michaelerule/goggles/hardware/pcb/Attiny14:24:84/eagle/index.html

### Index of eagle

../
board.zip
eagle.epf
gog2.b#1
gog2.b#2
gog2.brd
gog2.s#1
gog2.s#2
gog2.sch
Goggles.b#1
Goggles.brd
Goggles.s#1
Goggles.sch
goggles_eagle.zip
instructions
