michaelerule/goggles/tools/ee cheatsheet/media/circuitcheatsheet.odt

Circuit diagram cheat shee

t

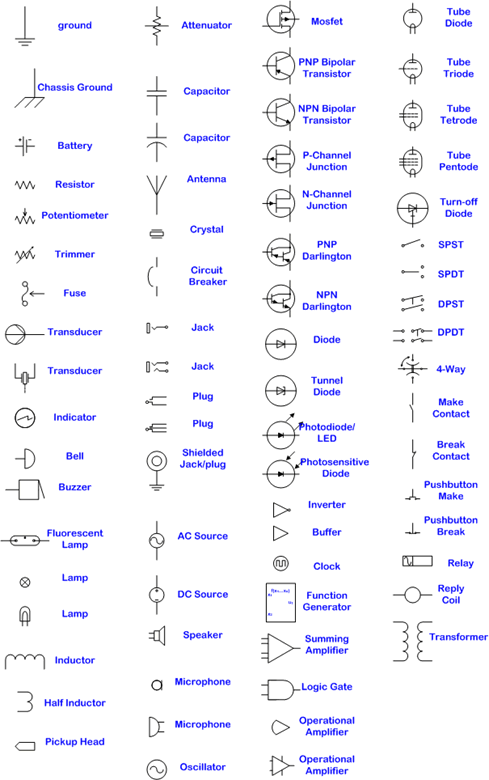
[picture p3: figure]
