michaelerule/goggles/tools/ee cheatsheet/media/LED.odt

LED and resistor cheat sheet

Wavelength (nm) | Color | Voltage | Resistor 3.3v | Resistor 5v
940 | Infrared | 1.5 | 100 | 180
880 | Infrared | 1.7 | 82 …
850 | Infrared
660 | Ultra Red | 1.8
635 | High Eff. Red | 2 | 68 … | 150
633 | Super Red | 2.2 | 56 …
620 | Super Orange
612 | Super Orange
605 | Orange | 2.1
595 | Super Yellow | 2.2
592 | Super Pure Yellow | 2.1
585 | Yellow
4500K | Incandescent White | 3.6 | none | 82 …
6500K | Pale White
8000K | Cool White
574 | Super Lime Yellow | 2.4 | 47 … | 150
570 | Super Lime Green | 2 | 68 …
565 | High Eff. Green | 2.1
560 | Super Pure Green
555 | Pure Green
525 | Aqua Green | 3.5 | none | 82 …
505 | Blue Green
470 | Super Blue | 3.6
430 | Ultra Blue | 3.8 | none | 68 …

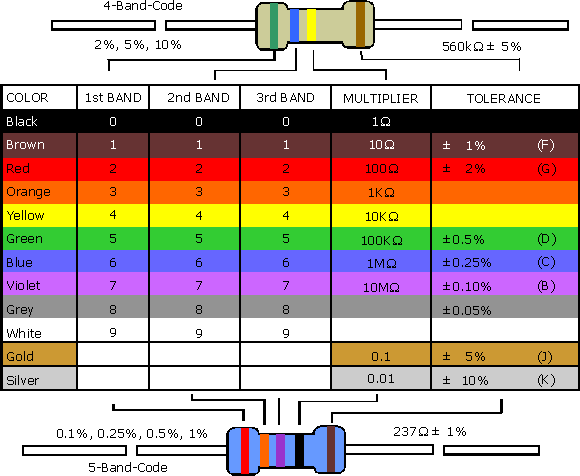
[picture p4: figure]
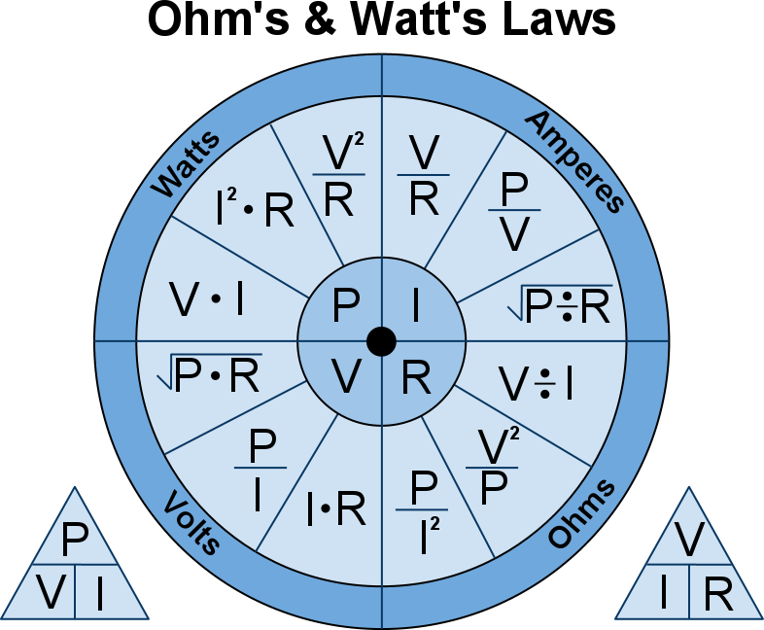
[picture p5: figure]
