michaelerule/goggles/documentation/laymanflicker/flicker_layman.odt

Geometric hallucinations induced by flickering light

Most people see colorful geometric patterns when looking at uniform flickering lights of a certain frequency. These patterns are subjectively described as “checkerboards” “ripples” “starbursts” “honeycombs”, sometimes taking on an overall tunnel-like appearance. It is striking how universal these patterns are – these simple flicker-induced geometric hallucinations are similar across individuals, and similar to certain visual hallucinations seen in visual-triggered epilepsy, migraine auras, and hallucinogens. A simple way to achieve such hallucinations is to close one's eyes and face toward the sun. Then, with fingers outstretched and separated, wave the hand back and forth in front of the eyes. Your fingers will create a flickering of the sunlight, which will be diffused and made uniform by closed eyelids.

The shortest primer on the brain and visual system ever

To understand why flickering lights might trigger geometric hallucinations, and why the hallucinations should take on particular forms, we need to understand a little about the nervous system. A good review is beyond the scope of this article, but I attempt to give a short overview here.

Very briefly, the eye and the brain contain cells called neurons which are specialized for computation. Neurons communicate with each other in little all-or-nothing events called action potentials or “spikes”, which propagate along long “wires” called axons, extending away from the cell body. These spikes are picked up by other neurons with more local tree of wires called “dendrites”. When discussing a large number of neurons, people sometime just think of their average “firing rate” or “activity”, rather than individual spikes.

Early visual processing relates to the sort of geometric hallucinations that we can get out of the early visual system. Light enters the eyes and is picked up by photoreceptor cells. These cells communicate to neurons in the retina that compress visual input. We will focus on four aspects of this compression related to flicker induced geometric visual hallucinations:

1. The RGB color-space picked up by the photo-receptors is converted to three contrasts : light-dark, yellow-blue, and red-green. The color-space conversion relates to how, for instance, a red-green flicker is especially effective at eliciting hallucinations.
2. The image is converted to a form focusing on edges and contrasts – uniform areas are ignored. This band-pass nature of early visual processing relates to how neurons are connected in the visual cortex, which in turns determines what size “waves” might appear in geometric visual hallucinations.
3. The retina has band-pass properties in time as well: slowly changing visual inputs are not registered. This is important for the temporal aspect of flicker induced hallucinations. Certain speeds of flickering will be picked up and transmitted better.
4. The eye has the greatest resolution in the very center, and the resolution drops off toward the periphery. This is why, for example, it is difficult to read things out of the corner of your eye. The brain also devotes less space to processing the periphery. The way that the visual field is “unfolded” in the brain determines the subjective appearance of spontaneous ( hallucinated ) neural activity.

A theory of geometric visual hallucinations

A theory on the origin of geometric visual hallucinations comes from Ermentrout and Cowen (1979), and briefly, makes the following hypotheses:

- The tunnel-like appearance of the overall hallucination relates to how the brain maps the visual field.
- Patterns like checkerboards and honeycombs arise from superposition of multiple waves
- Local interactions in the brain generate wave-like patterns of activity

The two halves of the visual field are split apart and each processed in one half of the brain. The brain devotes more processing power toward the center of the visual field. The net effect is to “unfold” the circular visual field from the retina into a “strip” of the brain at the back called the primary visual cortex. The result is that tunnel-like visual inputs map to simple regular patterns in the brain, and the inverse: hallucinated simple regular patterns in visual cortex are subjectively experienced as tunnel-like visual inputs.

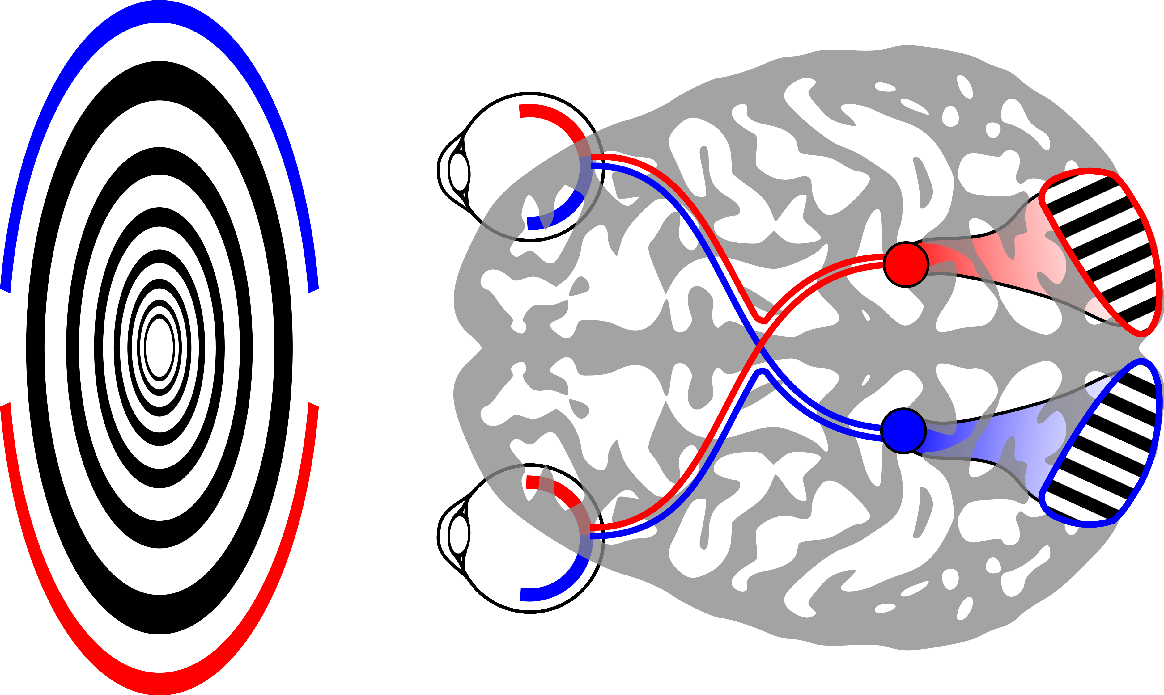
[picture p15: figure]
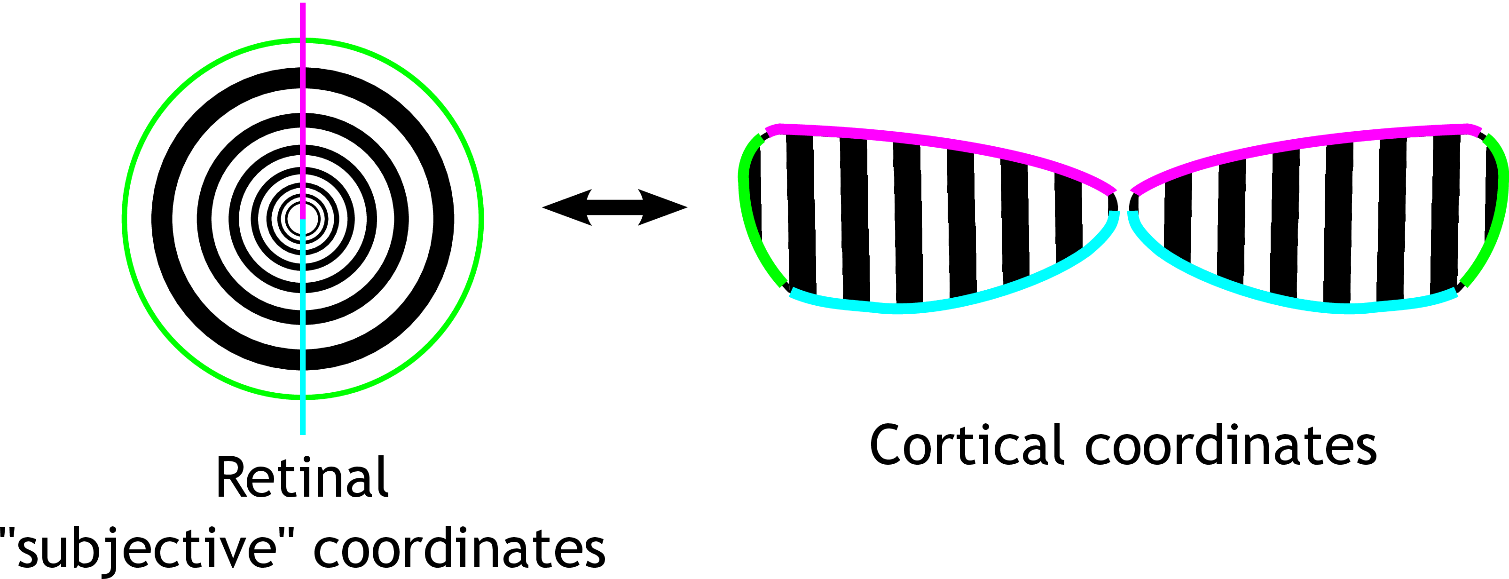
[picture p16: figure]

Stripe-like waves of activity in the brain are sufficient to explain circular, spiral, and starburst hallucinations. Checkerboards can be explained as the sum of two waves at right-angles, and honeycombs can be explains as the sum of three evenly spaced plane waves.

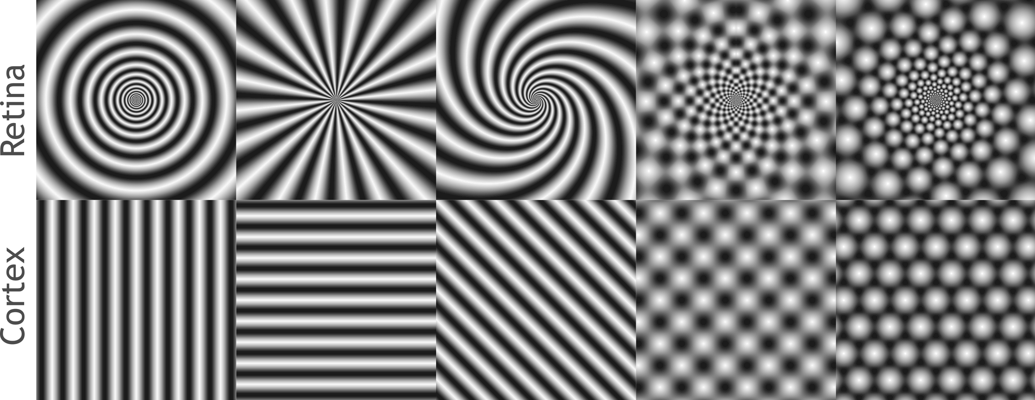
[picture p17: figure]

As to why the brain should spontaneously form waves of activity – that is something of an open question. Qualitatively, one can of it as the brain trying to “find” patterns in an image. Under certain circumstances, the pattern finding circuitry becomes unstable, and tends toward these simple, wave-like patterns.

Driving the brain with a uniform, flickering input

Flickering light is believed to excite patterns using a resonance effect that pushes visual cortex outside of its normal operation. Neural activity in the brain oscillates spontaneously. There is a natural 8-12Hz oscillation in the visual system called the “alpha rhythm”. Providing visual input at this frequency is believed to excite this intrinsic oscillation. Other frequencies work as well, and may interact with other intrinsic oscillations. Stimulation at 8-25Hz also works to excite the alpha oscillation. Even though this is twice the intrinsic frequency of the system, local patches of the brain are hypothesized to respond only to every-other oscillation cycle, effectively oscillating at alpha. These frequencies vary from person to person, and there may be other processes contributing to flicker hallucinations that we have yet to understand.

Why does making visual cortex “resonate” with a stimulus lead to pattern formation? The technical details of why this might happen are beyond the scope of this article – they involve assumptions about how neurons in visual cortex talk to each other, and mathematics to test whether patterned modes are favorable when forcing visual cortex with a uniform periodic stimulus. The qualitative idea is actually quite simple. For analogy, consider shaking a tray of water up and down. Even though you are forcing the whole tray uniformly, if you hit the right frequencies, you can create standing waves in the tray of water. The visual cortex does something similar when you hit it with flickering light.
