michaelerule/goggles/media/art/p (copy).png

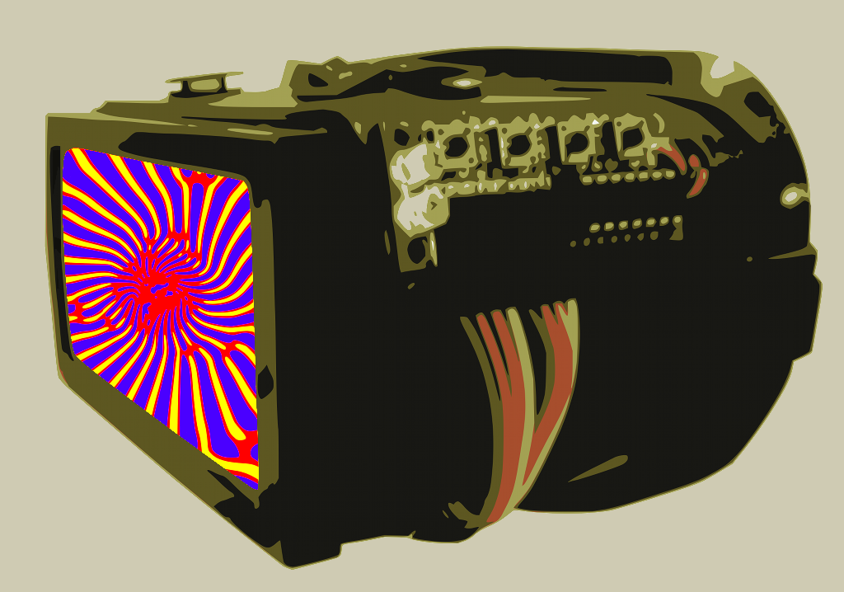
media/art/p (copy).png
