michaelerule/goggles/media/art/the goggs2.png

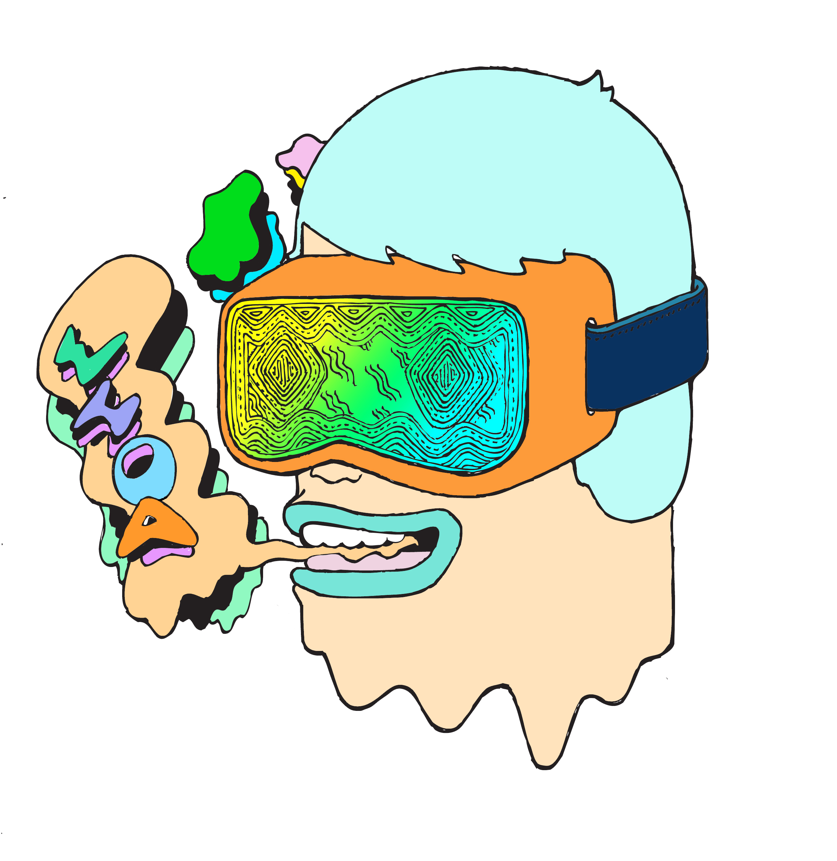
media/art/the goggs2.png
