michaelerule/goggles/media/artwork/2.png

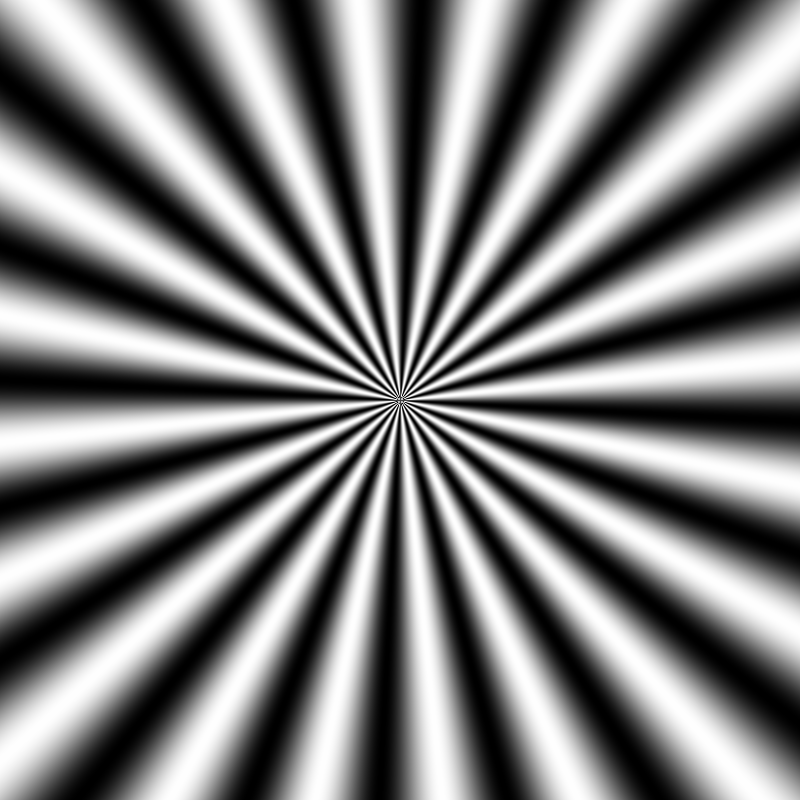
media/artwork/2.png
