michaelerule/goggles/media/artwork/3.png

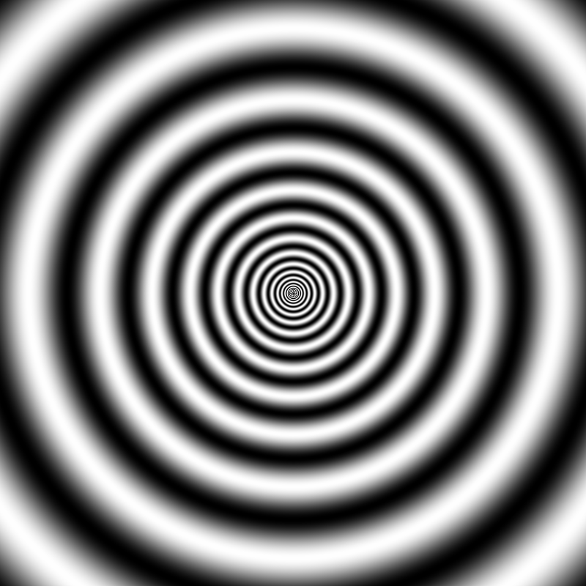
media/artwork/3.png
