michaelerule/goggles/media/artwork/4.png

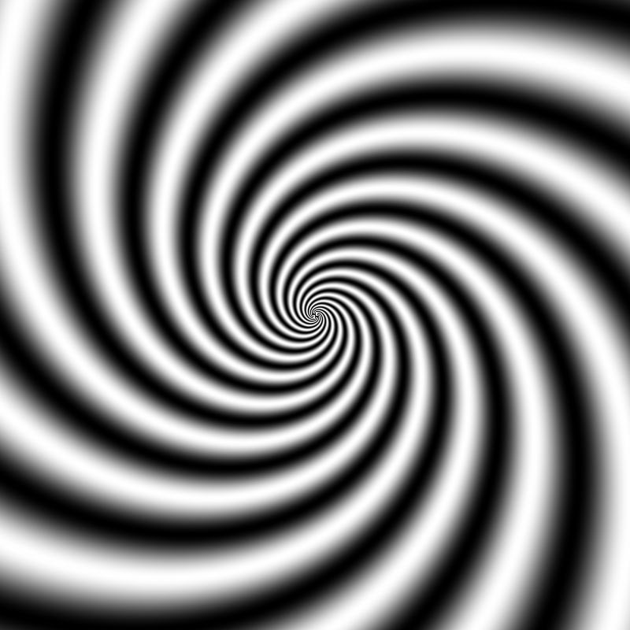
media/artwork/4.png
