michaelerule/goggles/media/artwork/DSCF3299 (copy).JPG

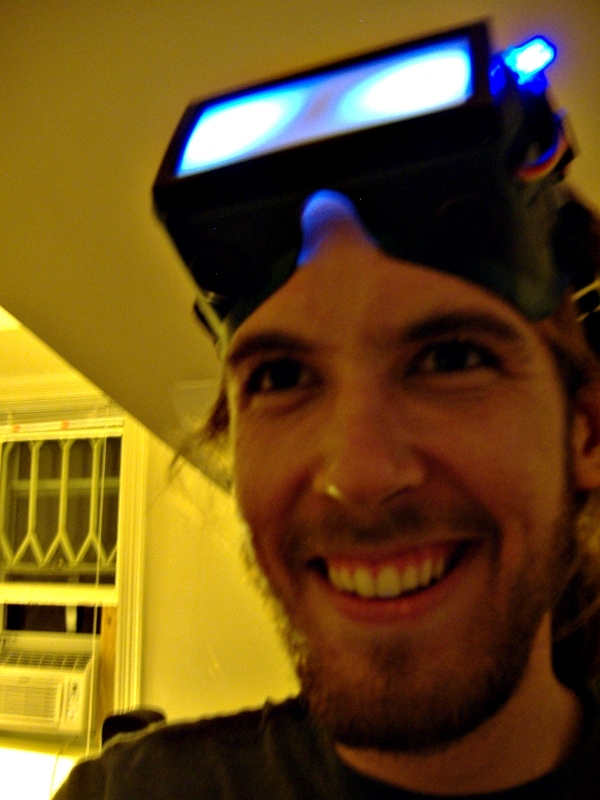
media/artwork/DSCF3299 (copy).JPG
