michaelerule/goggles/media/artwork/DSCF3302 (another copy).JPG.png

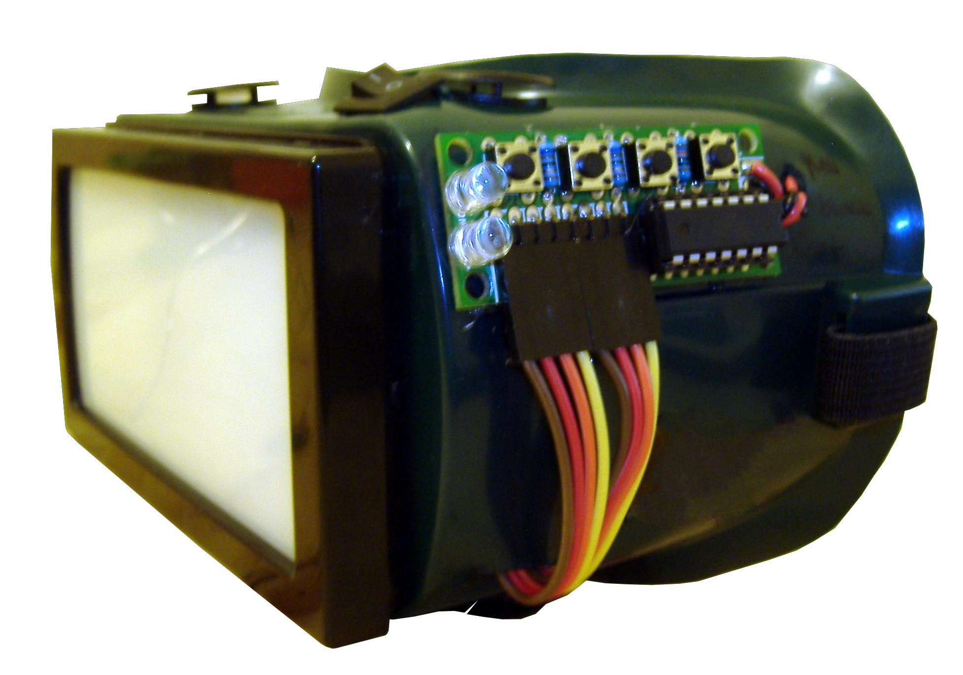
media/artwork/DSCF3302 (another copy).JPG.png
