michaelerule/goggles/media/artwork/out3-30109.png

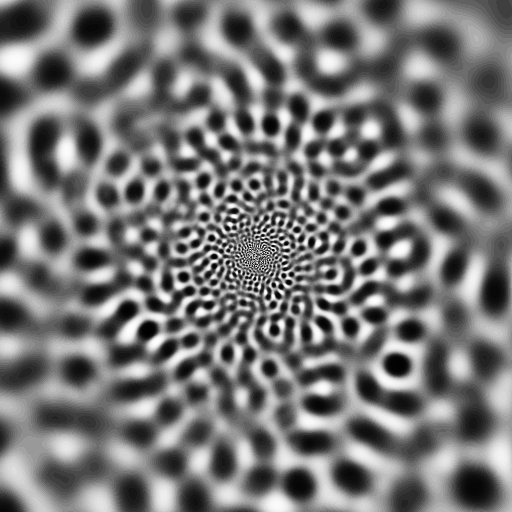
media/artwork/out3-30109.png
