michaelerule/goggles/media/artwork/out3-30433.png

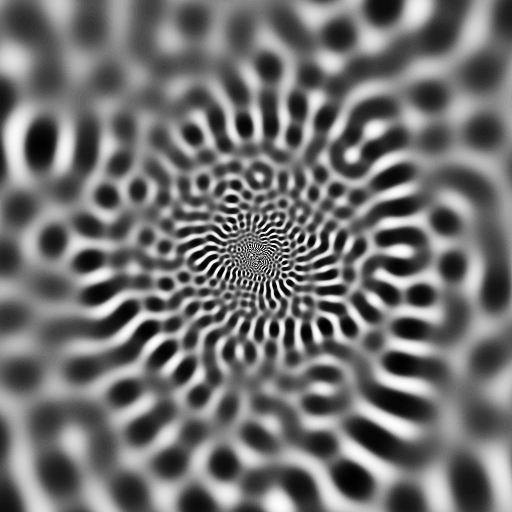
media/artwork/out3-30433.png
