michaelerule/goggles/media/artwork/out3-30541.png

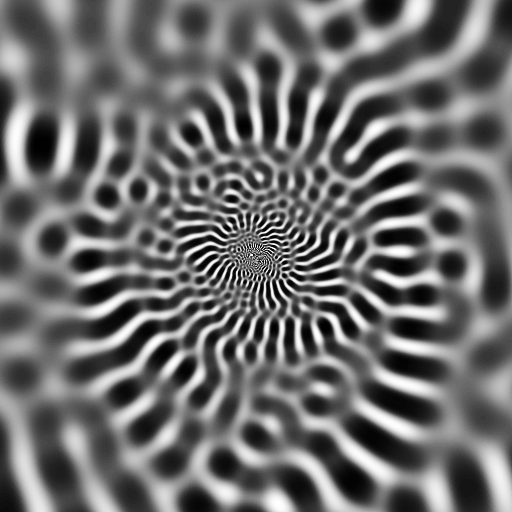
media/artwork/out3-30541.png
