michaelerule/goggles/media/artwork/out3-30649.png

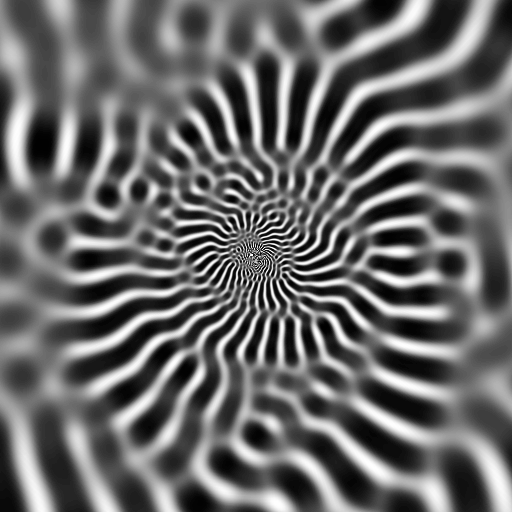
media/artwork/out3-30649.png
