michaelerule/goggles/media/artwork/out3-30757.png

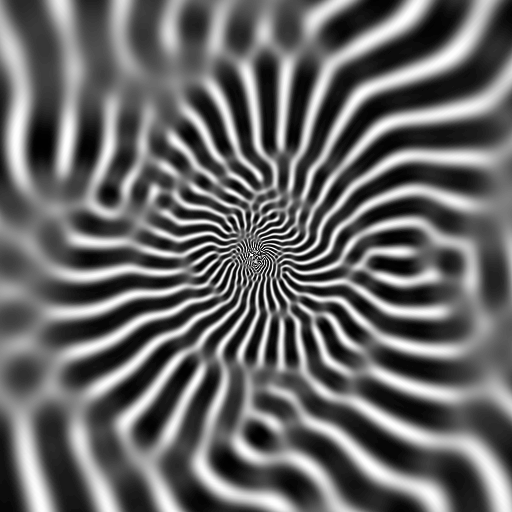
media/artwork/out3-30757.png
