michaelerule/goggles/media/artwork/out3-31729.png

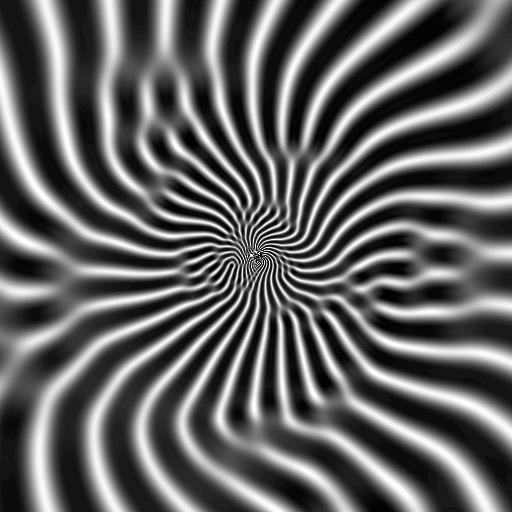
media/artwork/out3-31729.png
