michaelerule/goggles/media/artwork/theory.gif

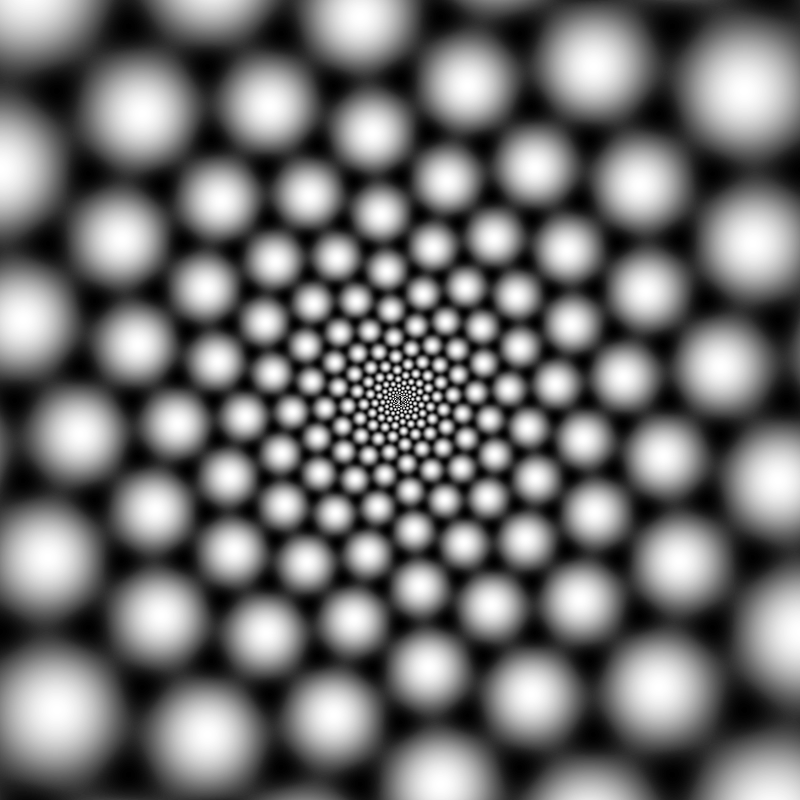
media/artwork/theory.gif
