michaelerule/goggles/media/photos/DSCF3150.JPG

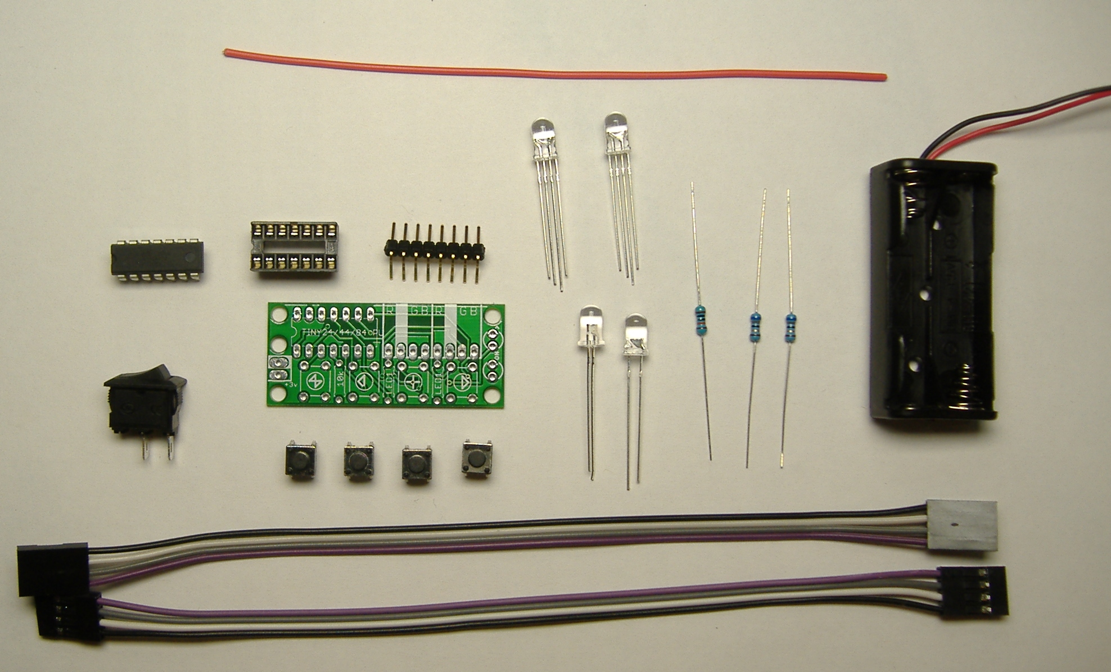
media/photos/DSCF3150.JPG
