michaelerule/goggles/media/photos/DSCF3152.JPG

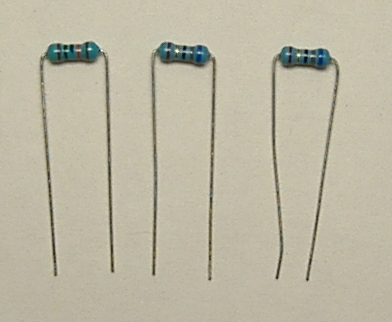
media/photos/DSCF3152.JPG
