michaelerule/goggles/media/photos/DSCF3153.JPG

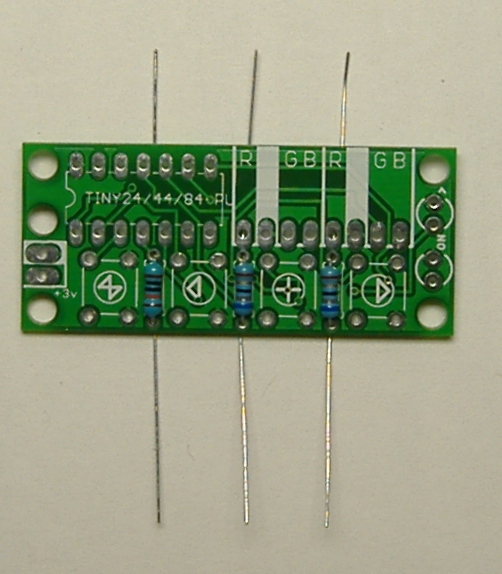
media/photos/DSCF3153.JPG
