michaelerule/goggles/media/photos/DSCF3162.JPG

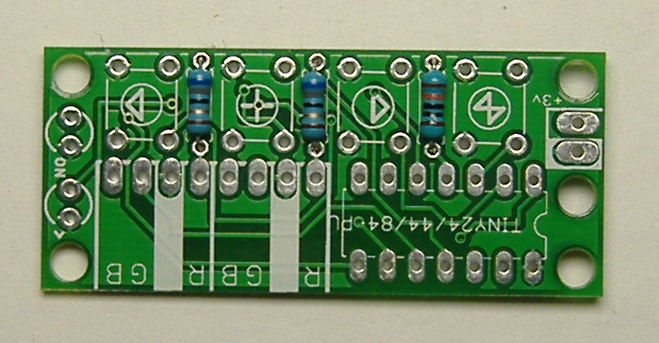
media/photos/DSCF3162.JPG
