michaelerule/goggles/media/photos/DSCF3163.JPG

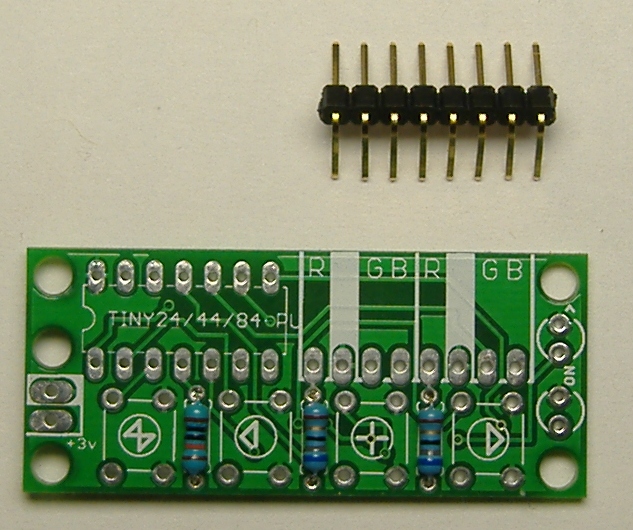
media/photos/DSCF3163.JPG
