michaelerule/goggles/media/photos/DSCF3164.JPG

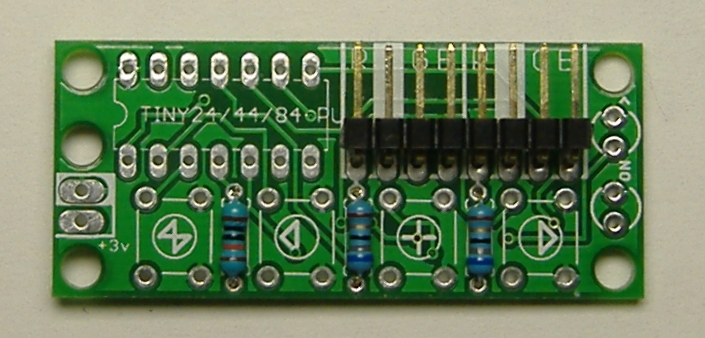
media/photos/DSCF3164.JPG
