michaelerule/goggles/media/photos/DSCF3165.JPG

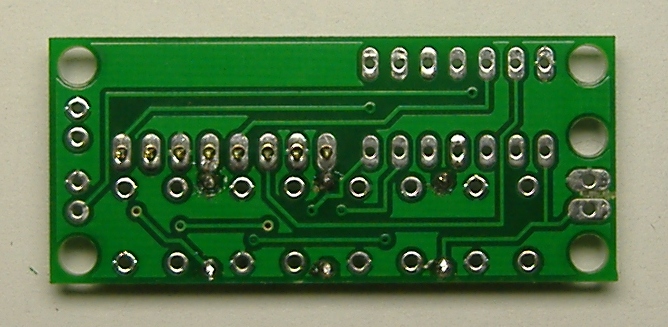
media/photos/DSCF3165.JPG
