michaelerule/goggles/media/photos/DSCF3166.JPG

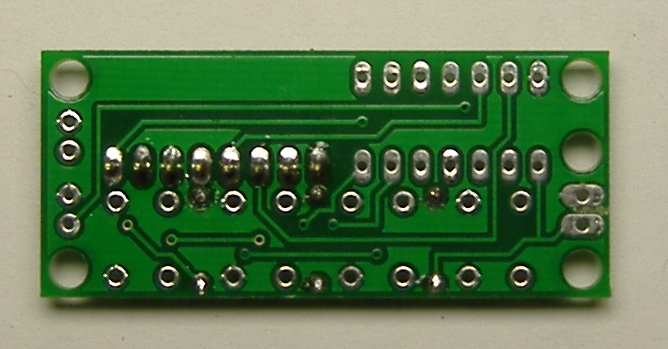
media/photos/DSCF3166.JPG
