michaelerule/goggles/media/photos/DSCF3168.JPG

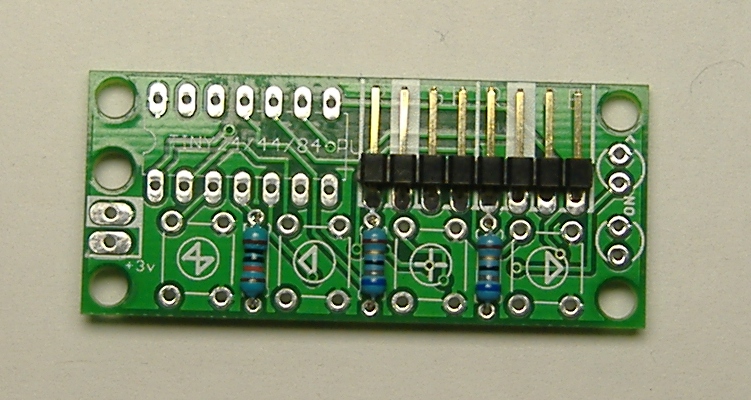
media/photos/DSCF3168.JPG
