michaelerule/goggles/media/photos/DSCF3169.JPG

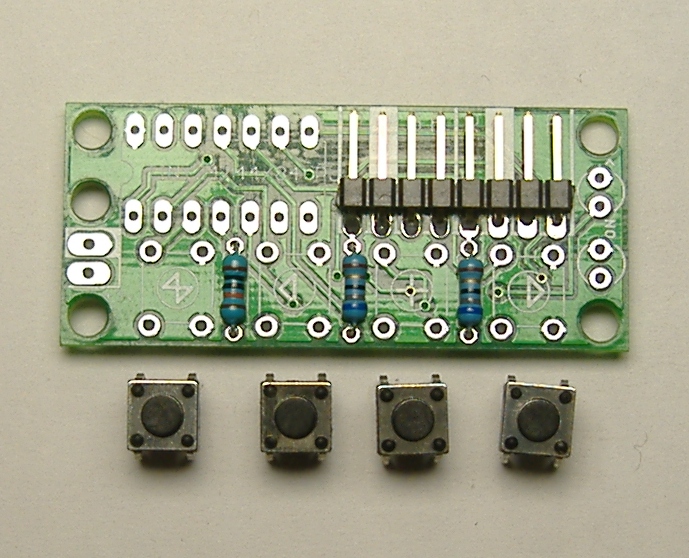
media/photos/DSCF3169.JPG
