michaelerule/goggles/media/photos/DSCF3172.JPG

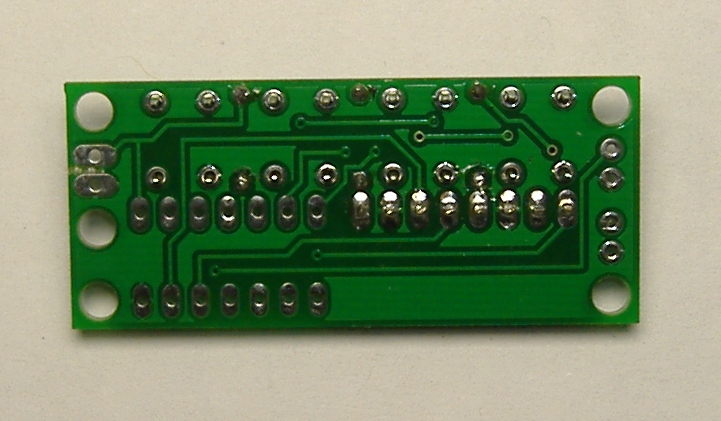
media/photos/DSCF3172.JPG
