michaelerule/goggles/media/photos/DSCF3175.JPG

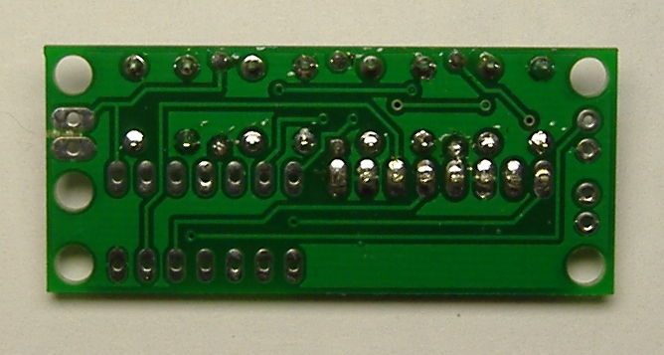
media/photos/DSCF3175.JPG
