michaelerule/goggles/media/photos/DSCF3176.JPG

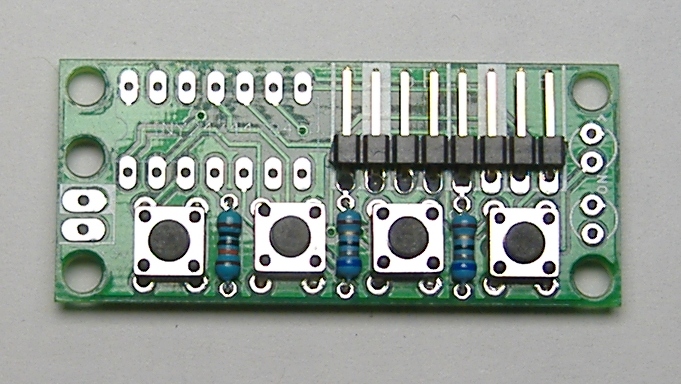
media/photos/DSCF3176.JPG
