michaelerule/goggles/media/photos/DSCF3177.JPG

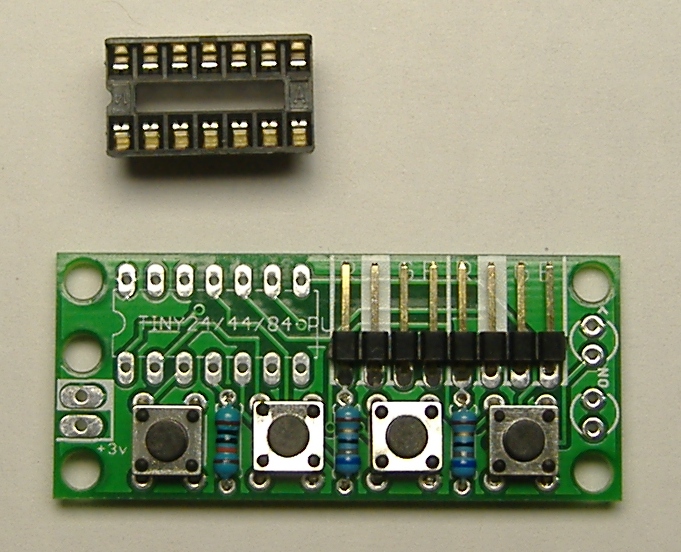
media/photos/DSCF3177.JPG
