michaelerule/goggles/media/photos/DSCF3188.JPG

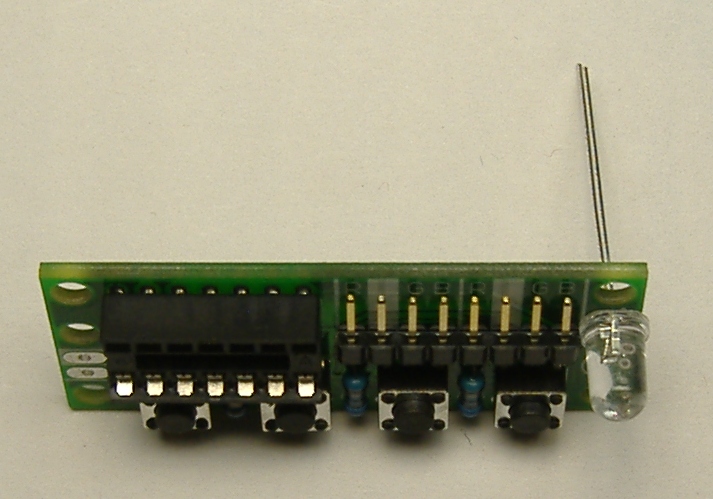
media/photos/DSCF3188.JPG
