michaelerule/goggles/media/photos/DSCF3192.JPG

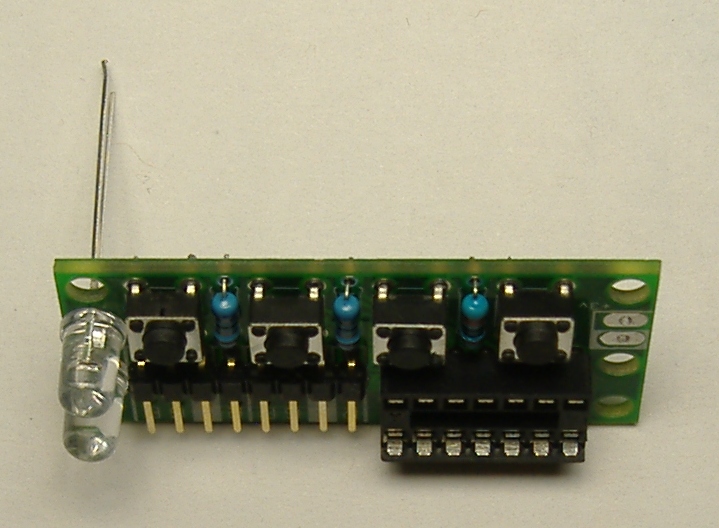
media/photos/DSCF3192.JPG
