michaelerule/goggles/media/photos/DSCF3194.JPG

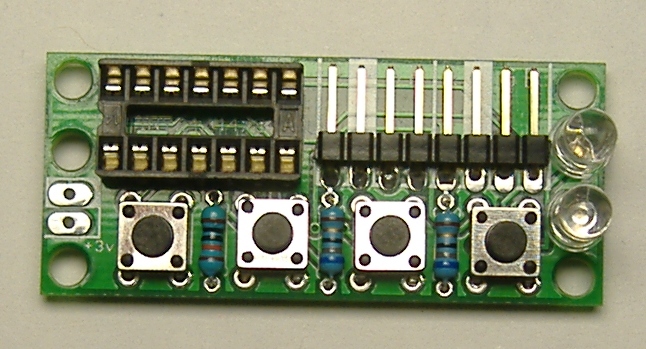
media/photos/DSCF3194.JPG
