michaelerule/goggles/media/photos/DSCF3197.JPG

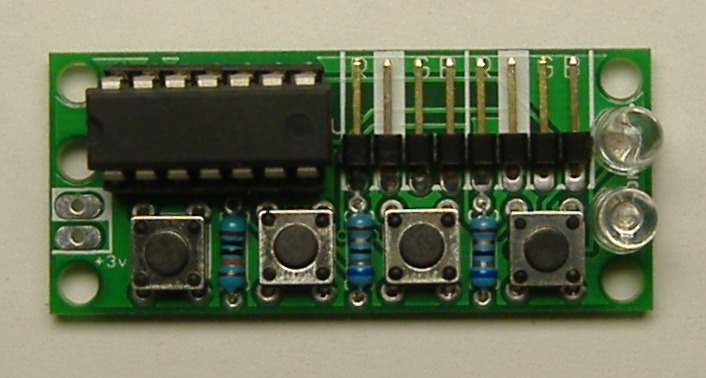
media/photos/DSCF3197.JPG
