michaelerule/goggles/media/photos/DSCF3198.JPG

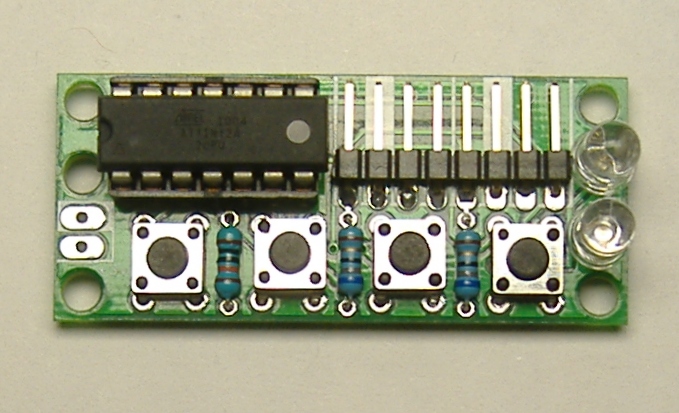
media/photos/DSCF3198.JPG
