michaelerule/goggles/media/photos/DSCF3199.JPG

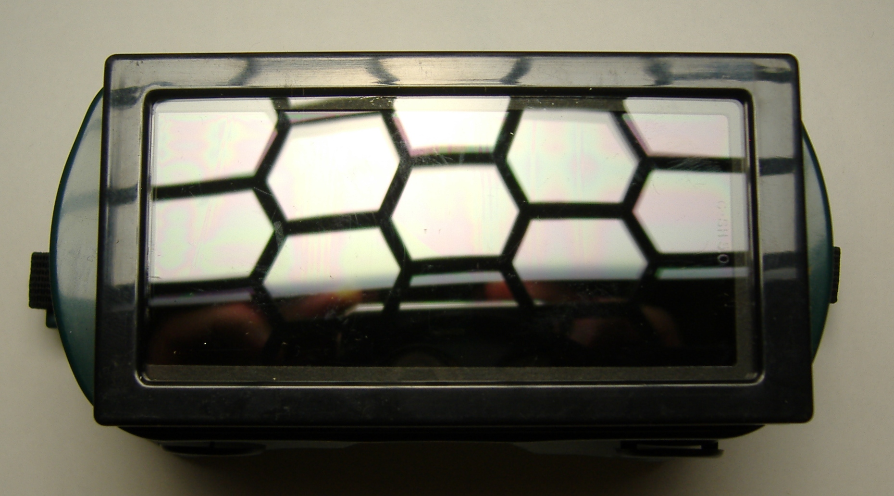
media/photos/DSCF3199.JPG
