michaelerule/goggles/media/photos/DSCF3201.JPG

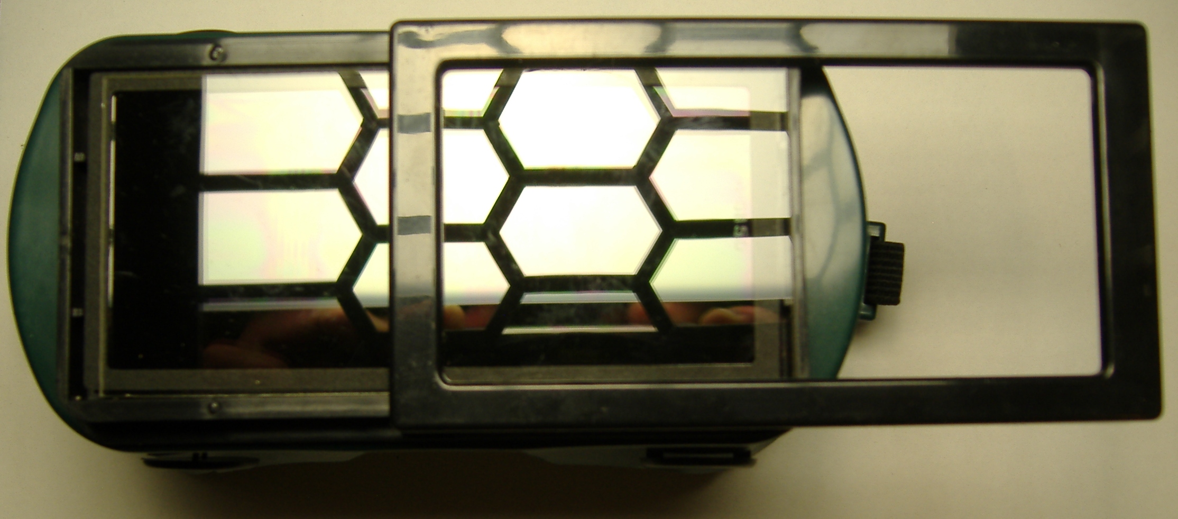
media/photos/DSCF3201.JPG
