michaelerule/goggles/media/photos/DSCF3202.JPG

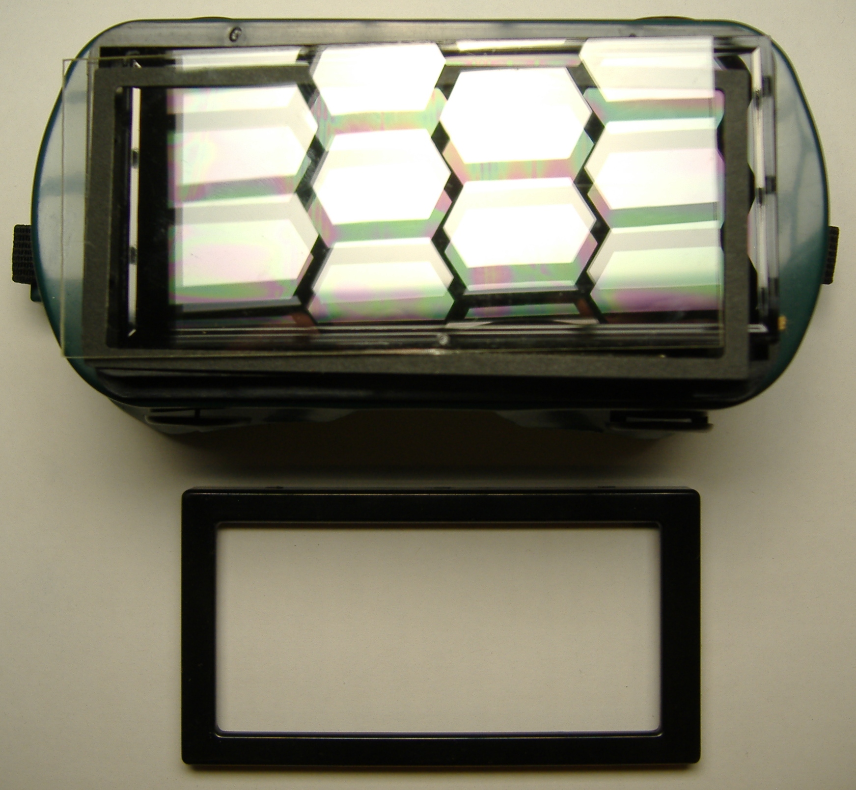
media/photos/DSCF3202.JPG
