michaelerule/goggles/media/photos/DSCF3203.JPG

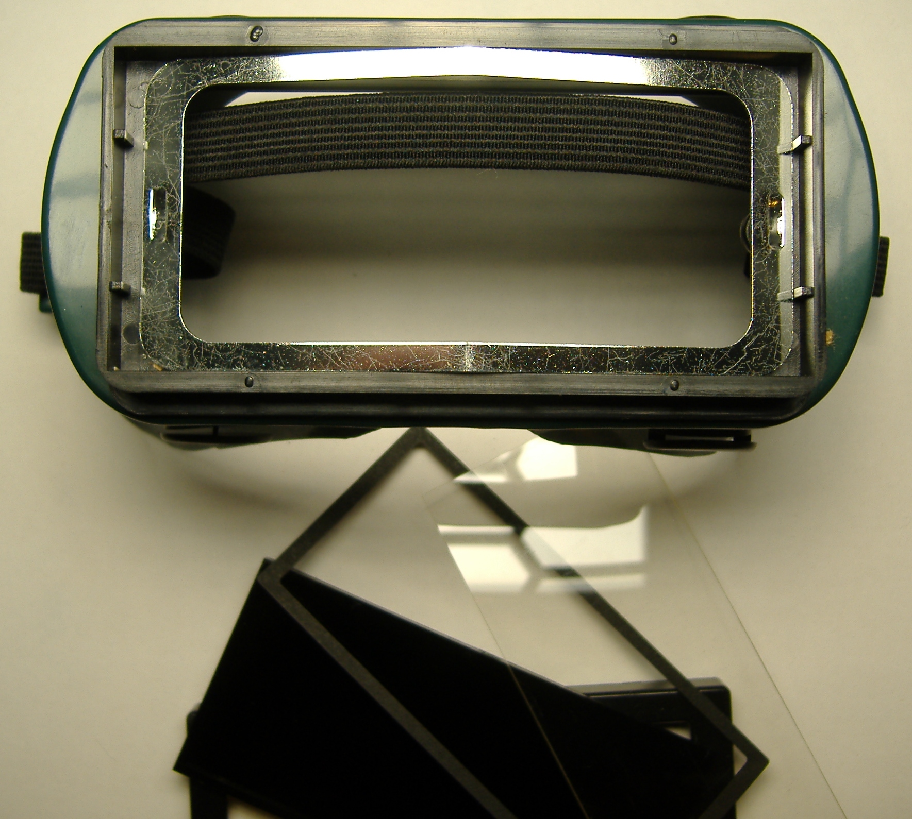
media/photos/DSCF3203.JPG
