michaelerule/goggles/media/photos/DSCF3205.JPG

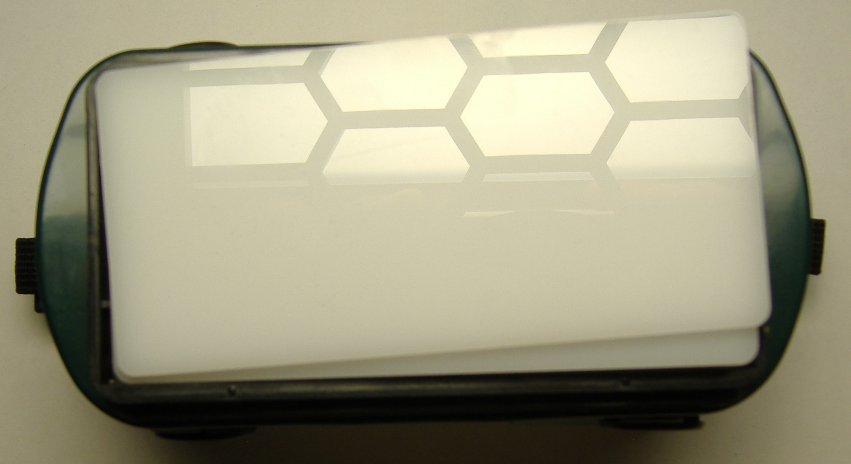
media/photos/DSCF3205.JPG
