michaelerule/goggles/media/photos/DSCF3206.JPG

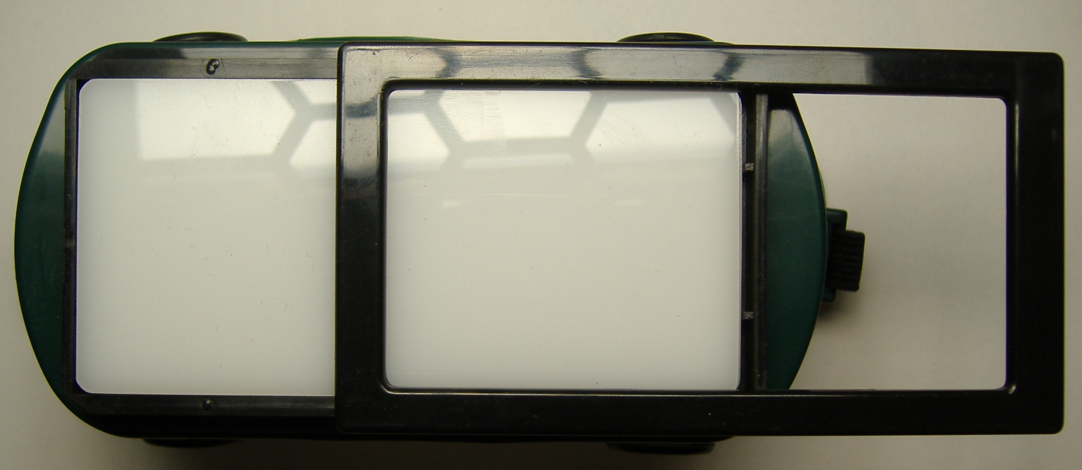
media/photos/DSCF3206.JPG
