michaelerule/goggles/media/photos/DSCF3207.JPG

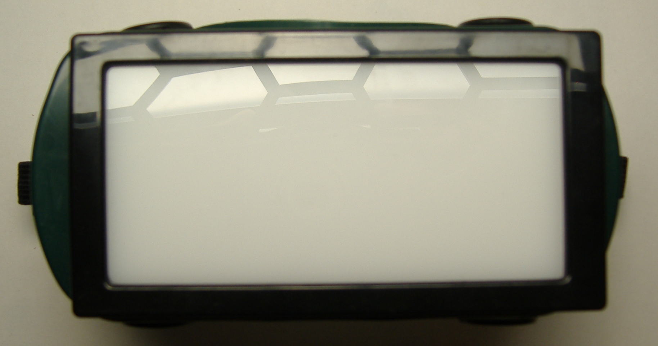
media/photos/DSCF3207.JPG
