michaelerule/goggles/media/photos/DSCF3210.JPG

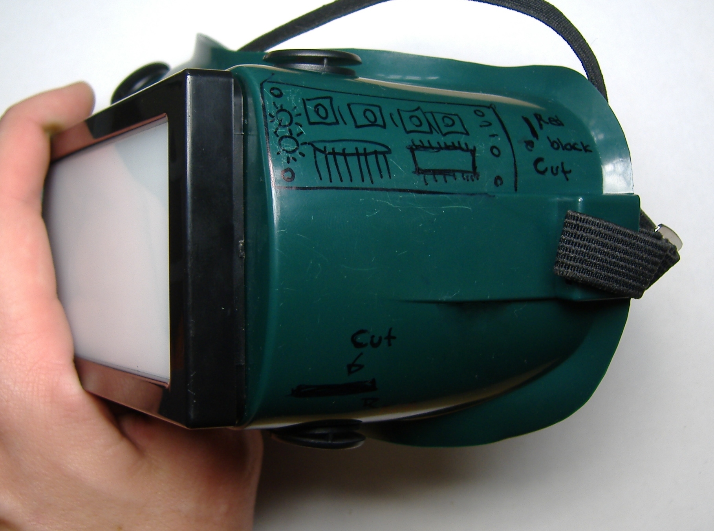
media/photos/DSCF3210.JPG
