michaelerule/goggles/media/photos/DSCF3211.JPG

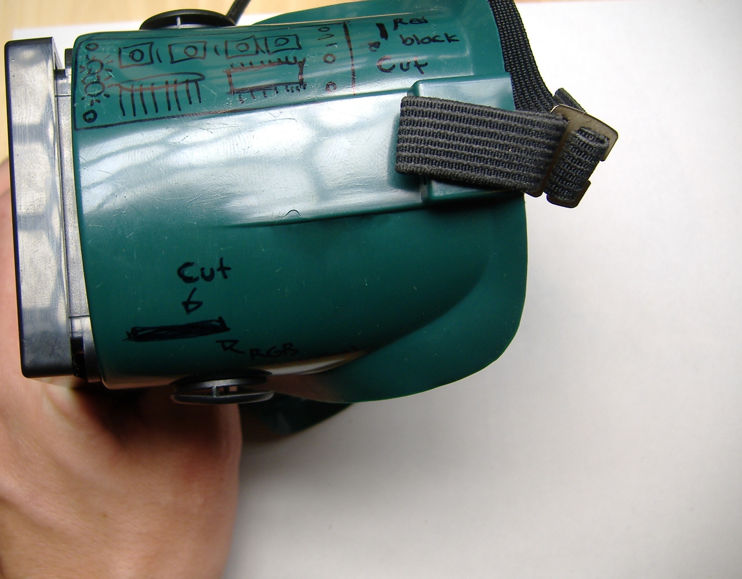
media/photos/DSCF3211.JPG
