michaelerule/goggles/media/photos/DSCF3214.JPG

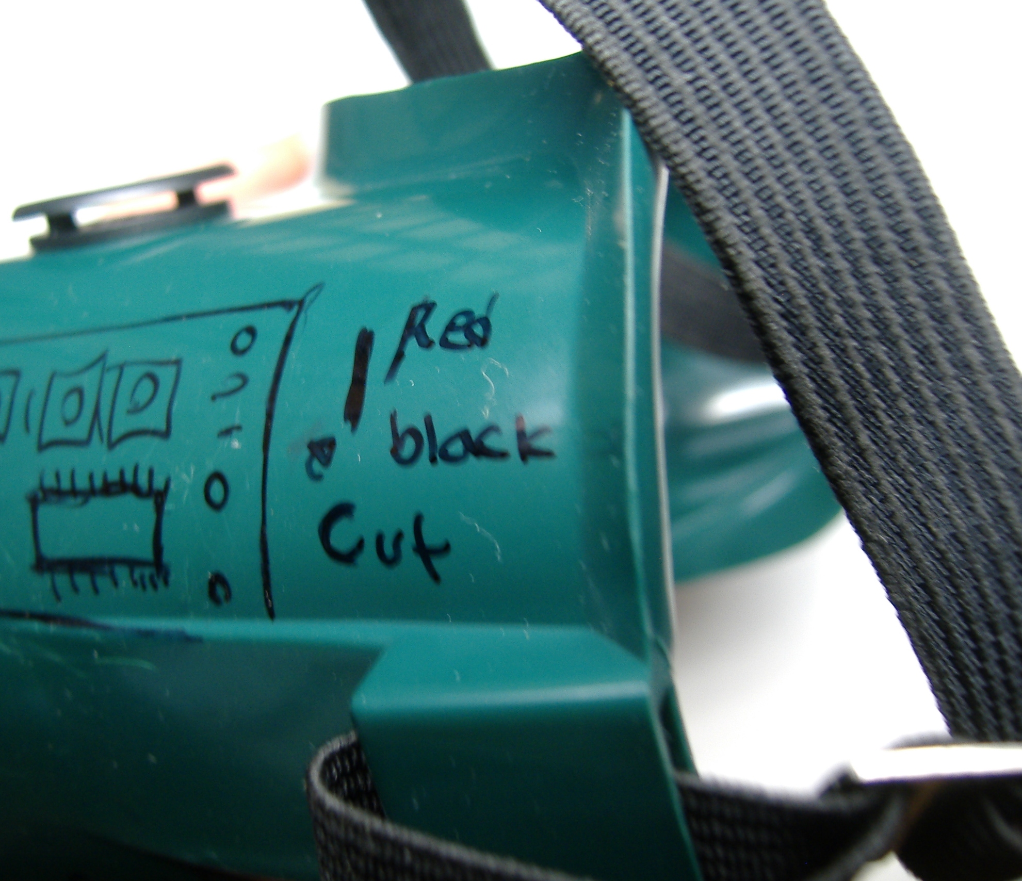
media/photos/DSCF3214.JPG
