michaelerule/goggles/media/photos/DSCF3215.JPG

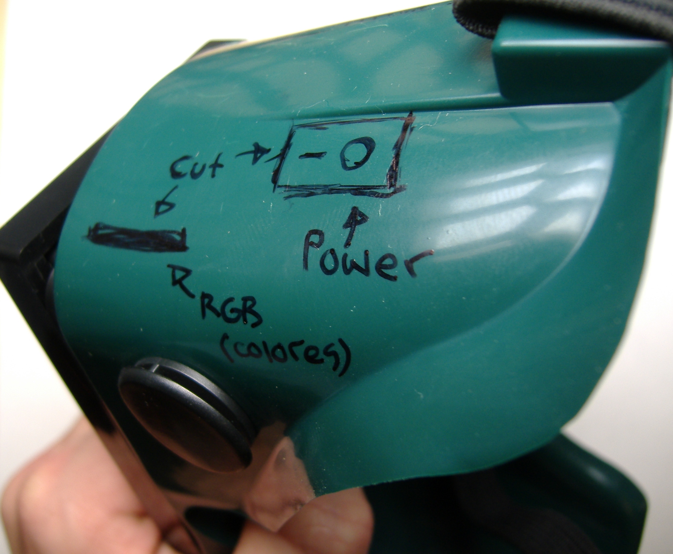
media/photos/DSCF3215.JPG
