michaelerule/goggles/media/photos/DSCF3216.JPG

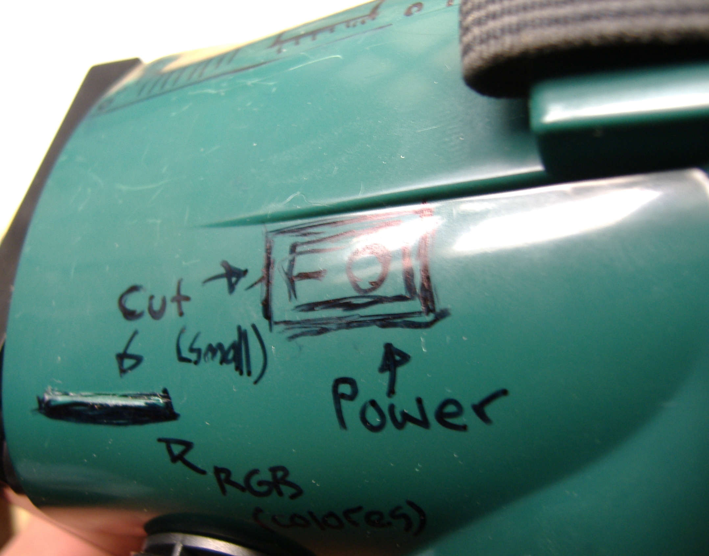
media/photos/DSCF3216.JPG
