michaelerule/goggles/media/photos/DSCF3218.JPG

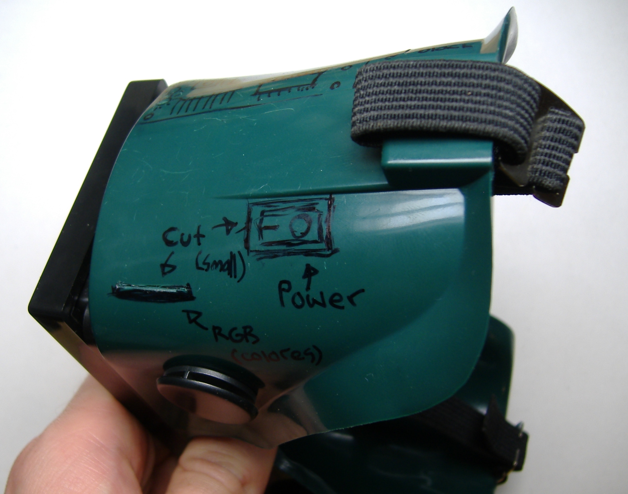
media/photos/DSCF3218.JPG
