michaelerule/goggles/media/photos/DSCF3219.JPG

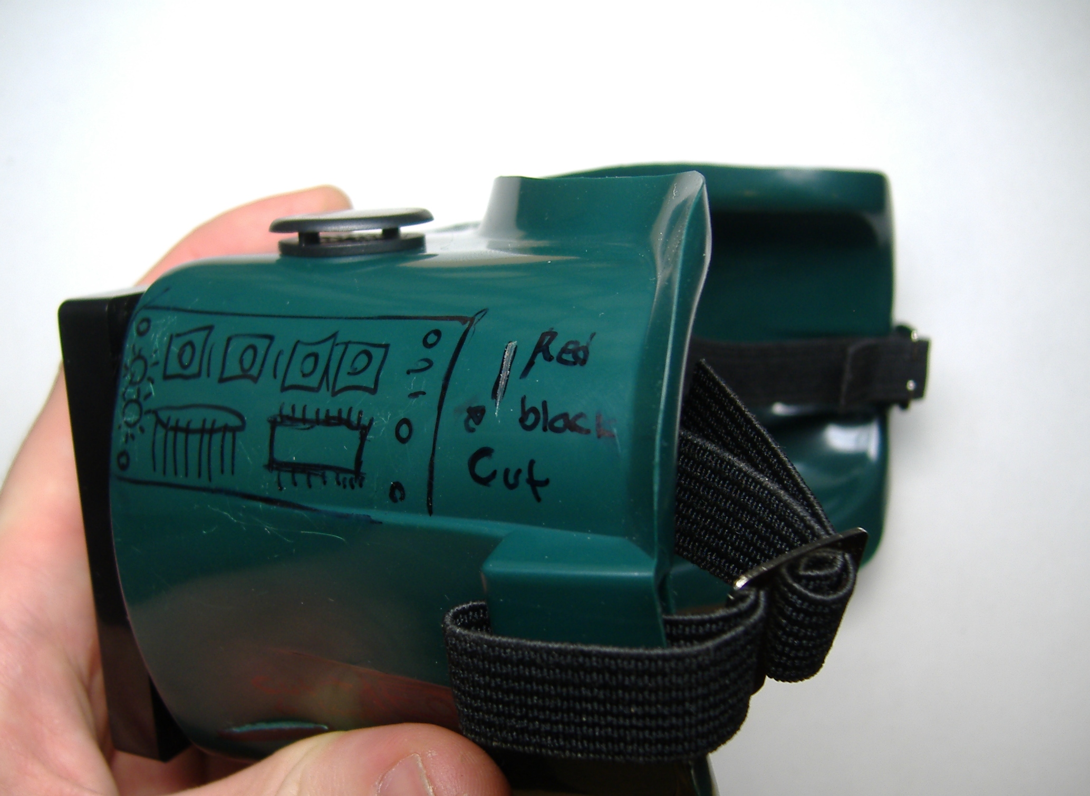
media/photos/DSCF3219.JPG
