michaelerule/goggles/media/photos/DSCF3220.JPG

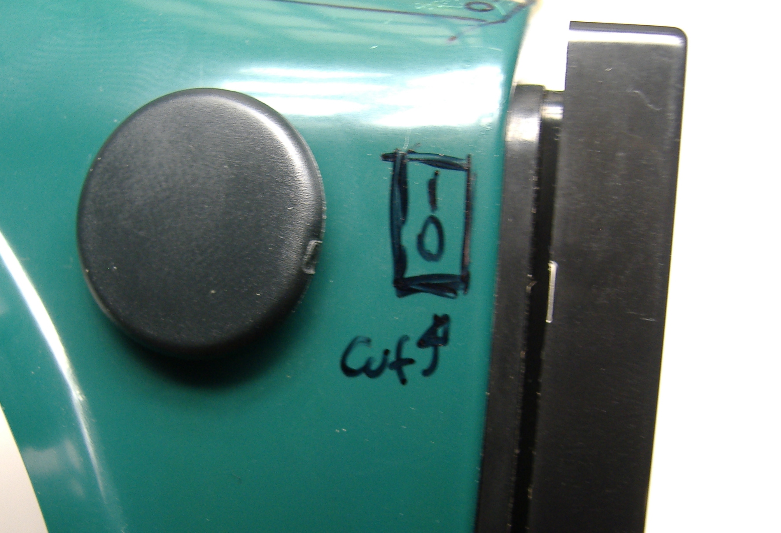
media/photos/DSCF3220.JPG
