michaelerule/goggles/media/photos/DSCF3221.JPG

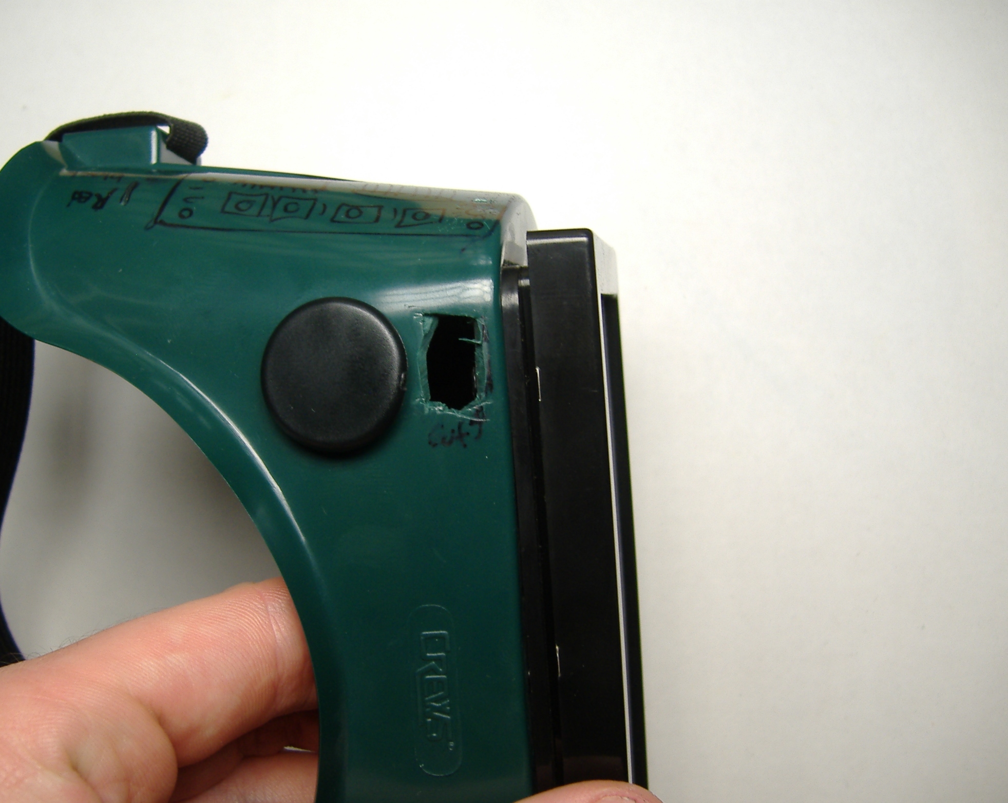
media/photos/DSCF3221.JPG
