michaelerule/goggles/media/photos/DSCF3222.JPG

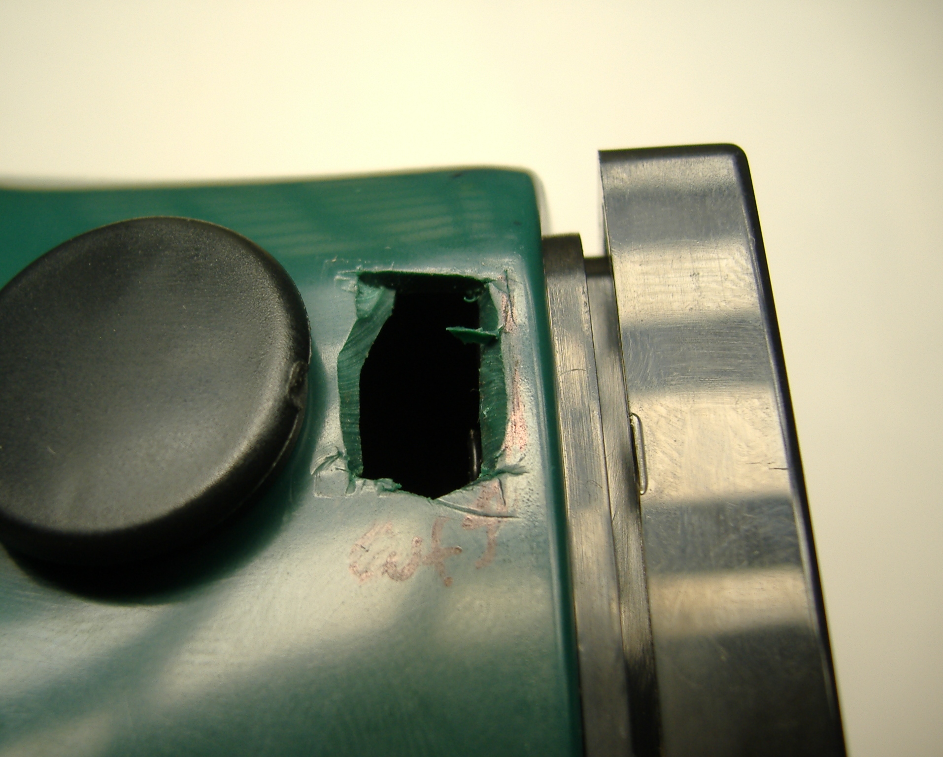
media/photos/DSCF3222.JPG
