michaelerule/goggles/media/photos/DSCF3226.JPG

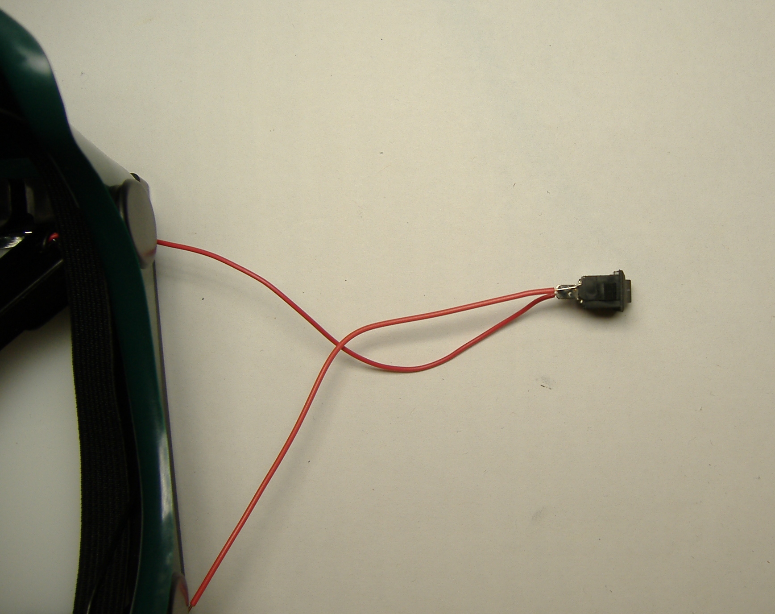
media/photos/DSCF3226.JPG
