michaelerule/goggles/media/photos/DSCF3229.JPG

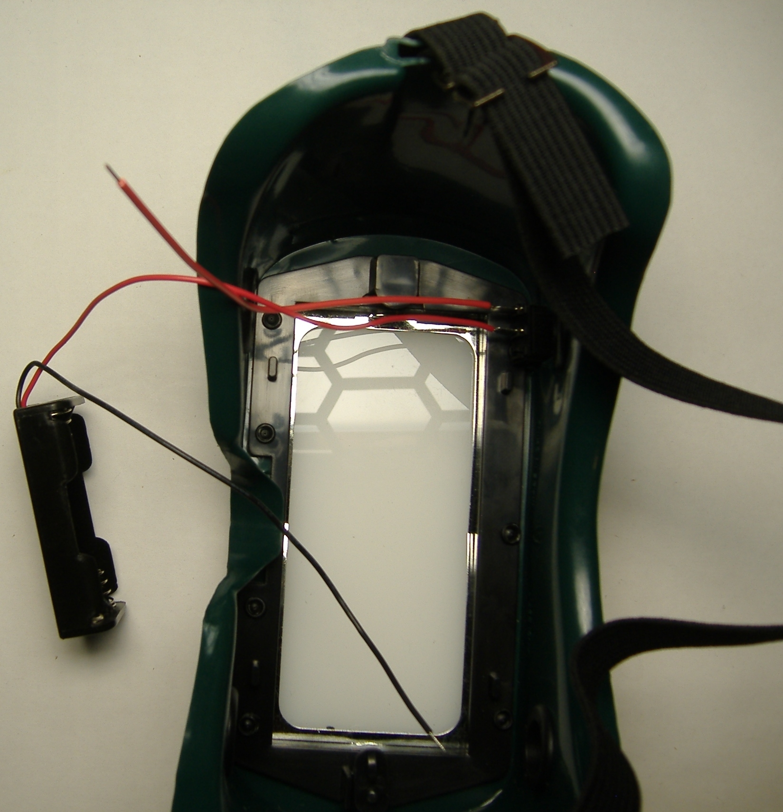
media/photos/DSCF3229.JPG
