michaelerule/goggles/media/photos/DSCF3235.JPG

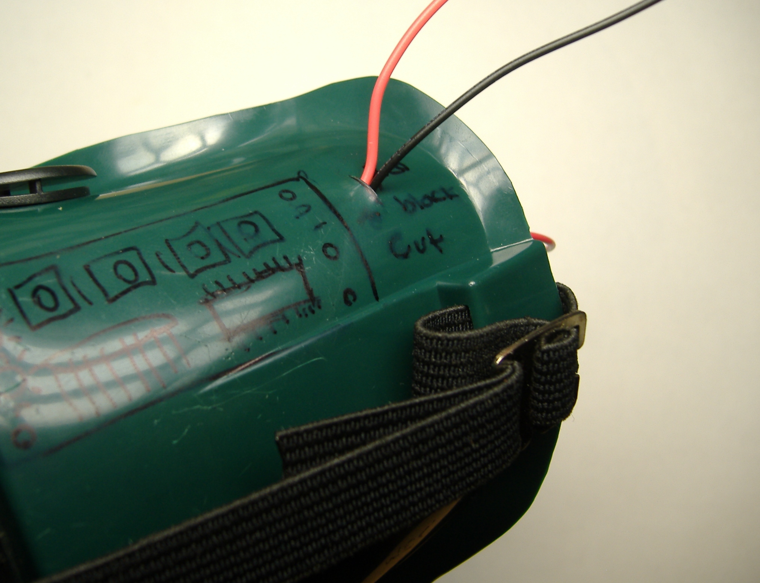
media/photos/DSCF3235.JPG
