michaelerule/goggles/media/photos/DSCF3238.JPG

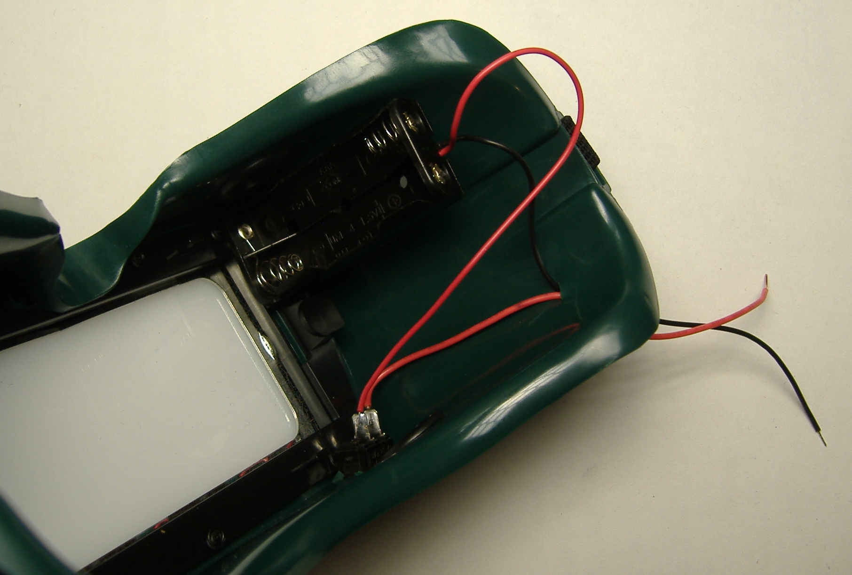
media/photos/DSCF3238.JPG
