michaelerule/goggles/media/photos/DSCF3239.JPG

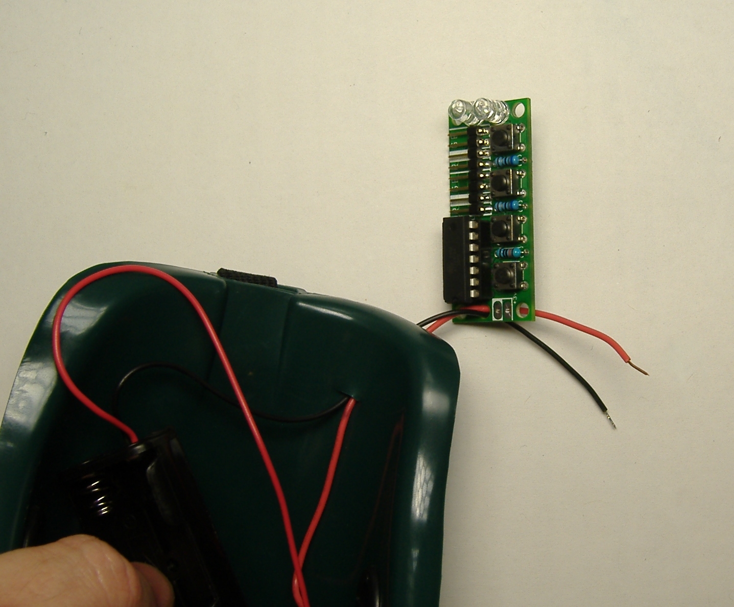
media/photos/DSCF3239.JPG
