michaelerule/goggles/media/photos/DSCF3245.JPG

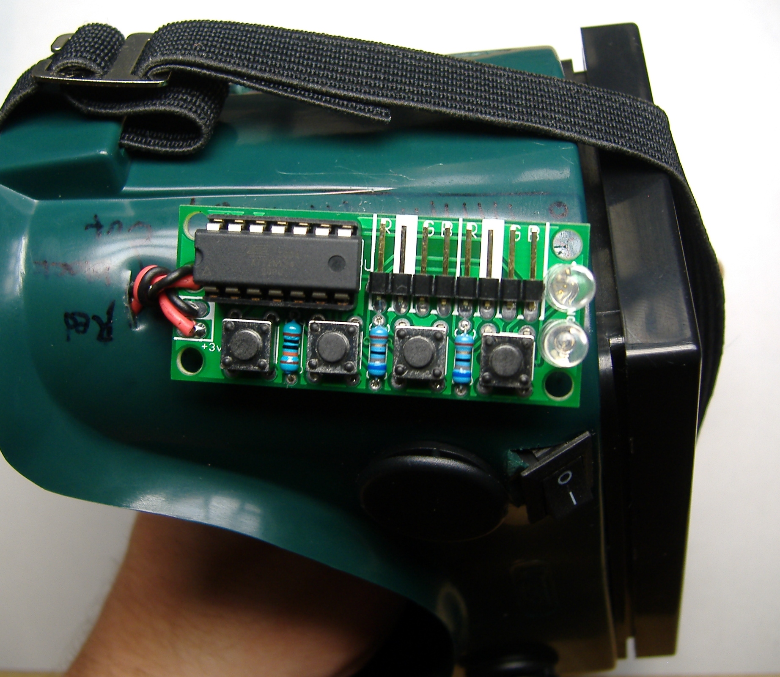
media/photos/DSCF3245.JPG
