michaelerule/goggles/media/photos/DSCF3246.JPG

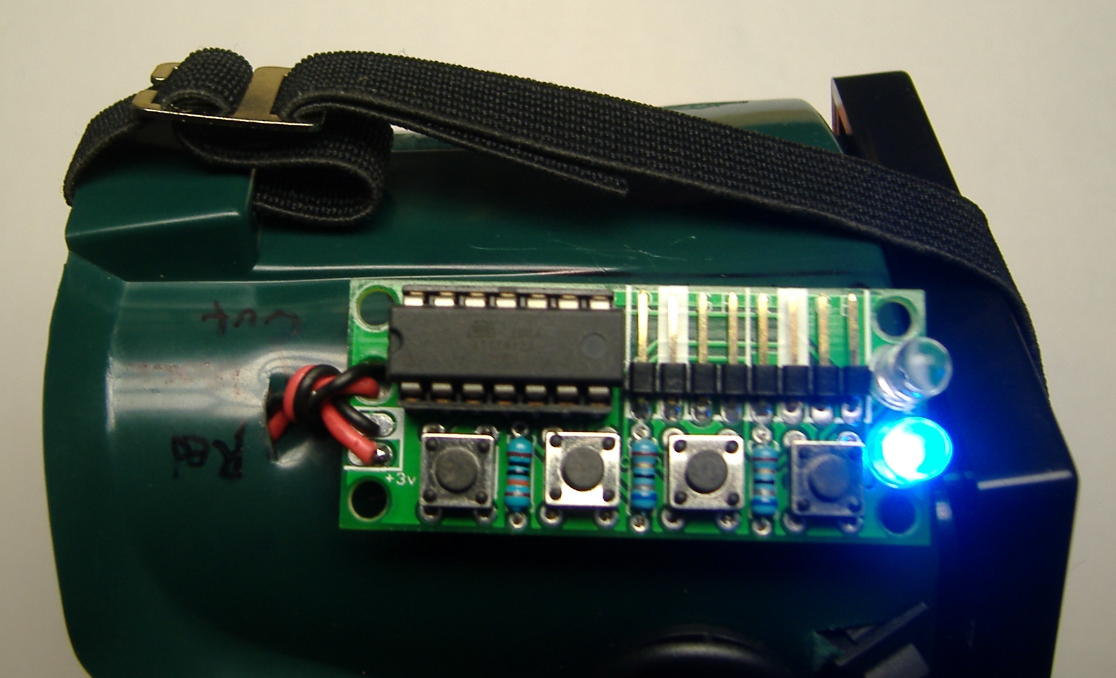
media/photos/DSCF3246.JPG
