michaelerule/goggles/media/photos/DSCF3250.JPG

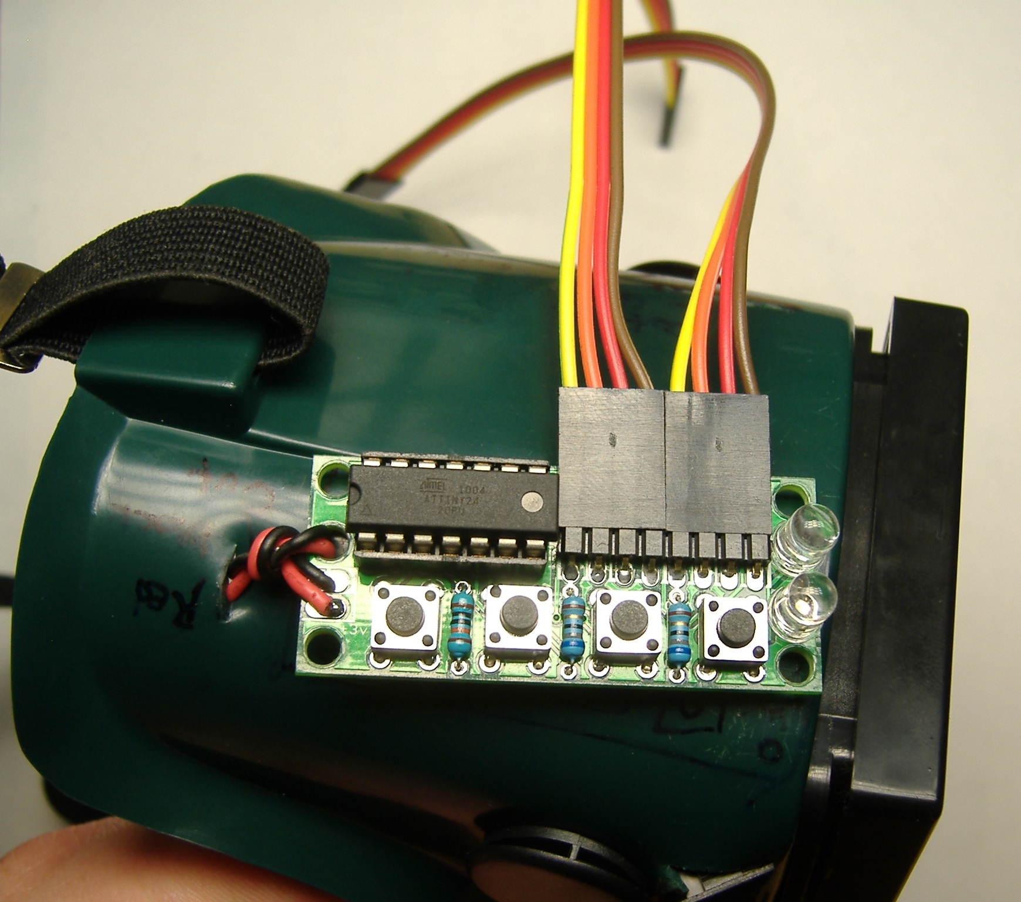
media/photos/DSCF3250.JPG
