michaelerule/goggles/media/photos/DSCF3254.JPG

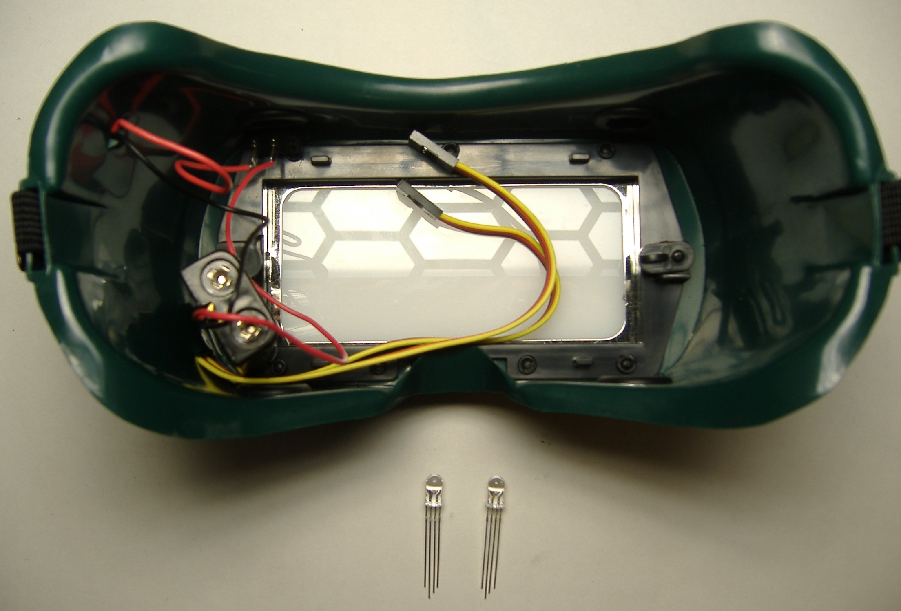
media/photos/DSCF3254.JPG
