michaelerule/goggles/media/photos/DSCF3255.JPG

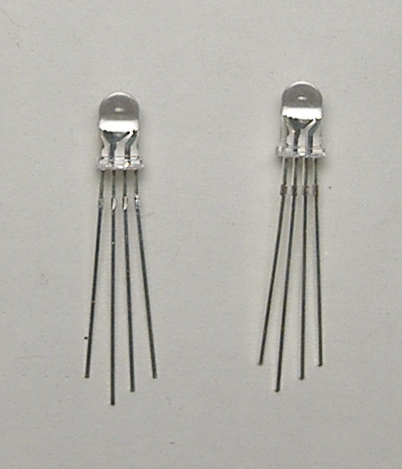
media/photos/DSCF3255.JPG
