michaelerule/goggles/media/photos/DSCF3256.JPG

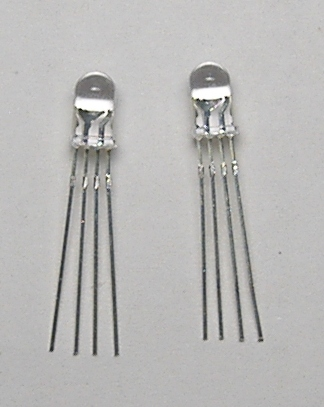
media/photos/DSCF3256.JPG
