michaelerule/goggles/media/photos/DSCF3257.JPG

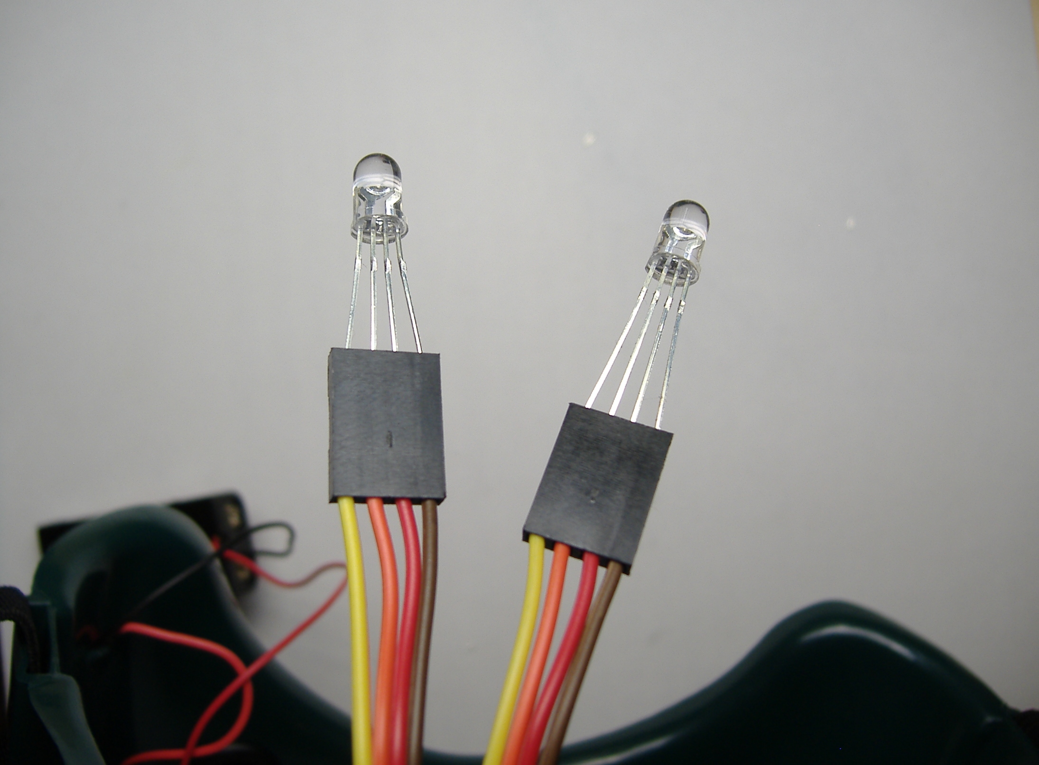
media/photos/DSCF3257.JPG
