michaelerule/goggles/media/photos/DSCF3258.JPG

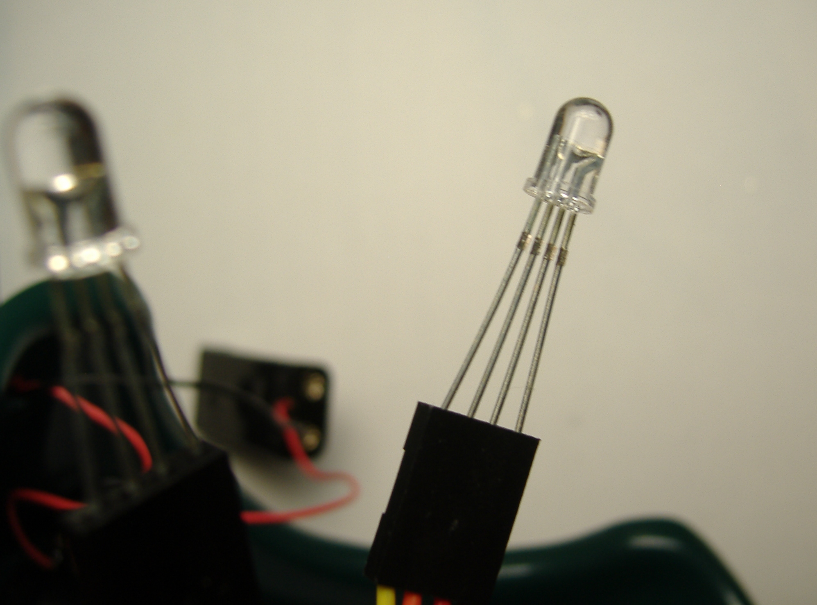
media/photos/DSCF3258.JPG
