michaelerule/goggles/media/photos/DSCF3259.JPG

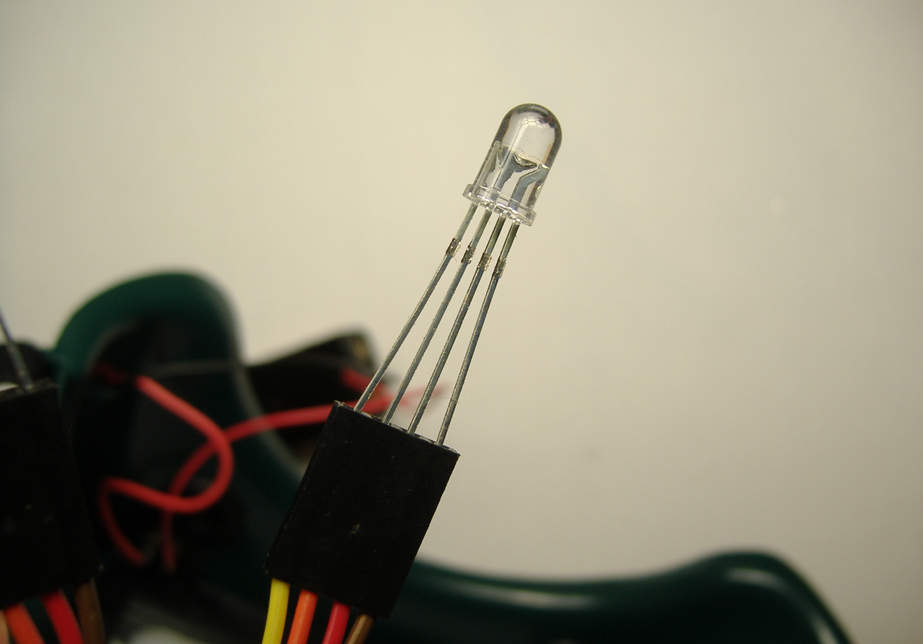
media/photos/DSCF3259.JPG
