michaelerule/goggles/media/photos/DSCF3260.JPG

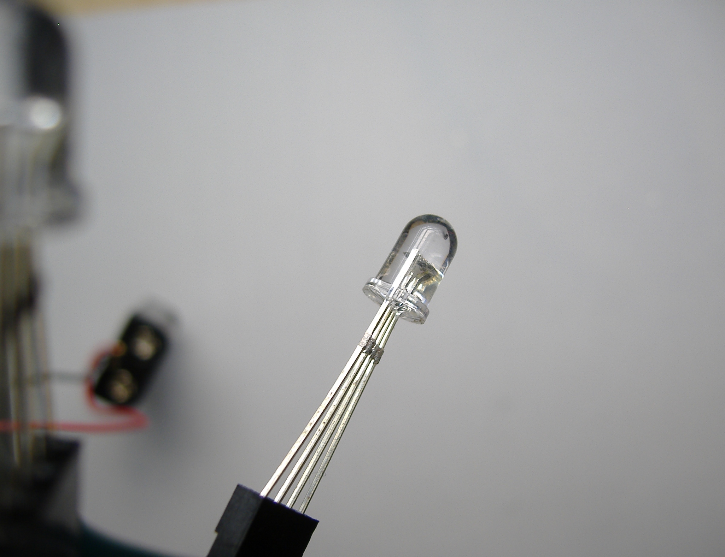
media/photos/DSCF3260.JPG
