michaelerule/goggles/media/photos/DSCF3263.JPG

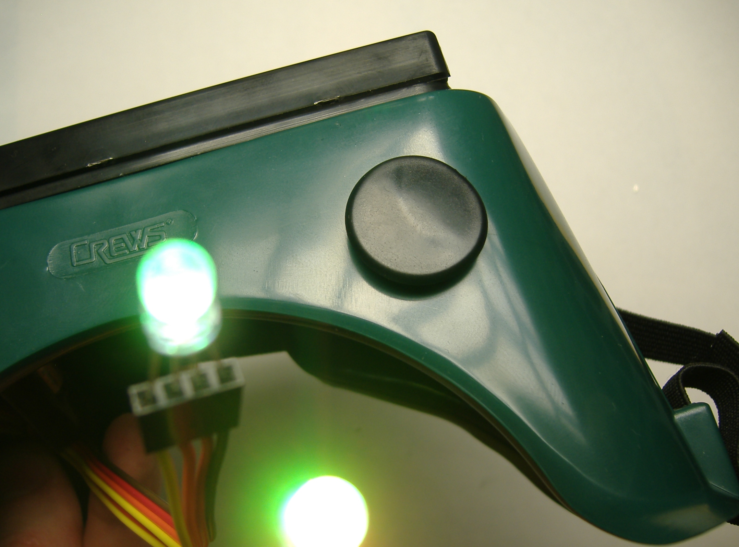
media/photos/DSCF3263.JPG
