michaelerule/goggles/media/photos/DSCF3264.JPG

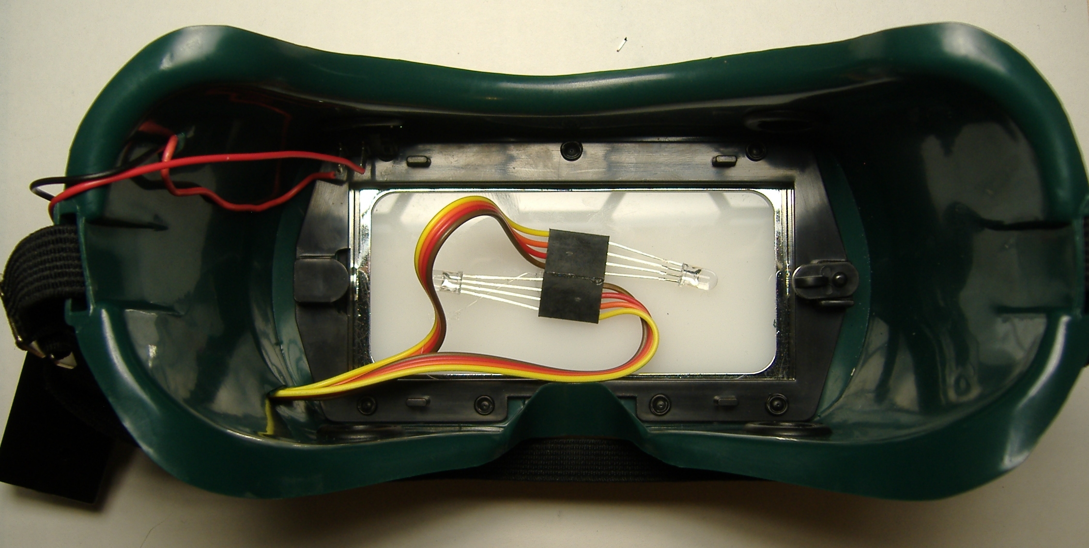
media/photos/DSCF3264.JPG
