michaelerule/goggles/media/photos/DSCF3266.JPG

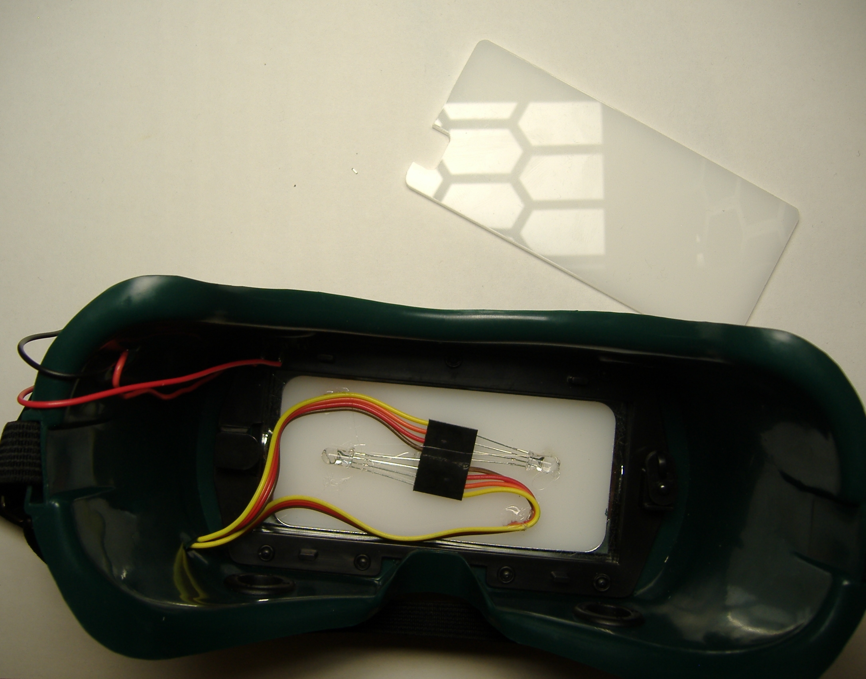
media/photos/DSCF3266.JPG
