michaelerule/goggles/media/photos/DSCF3269.JPG

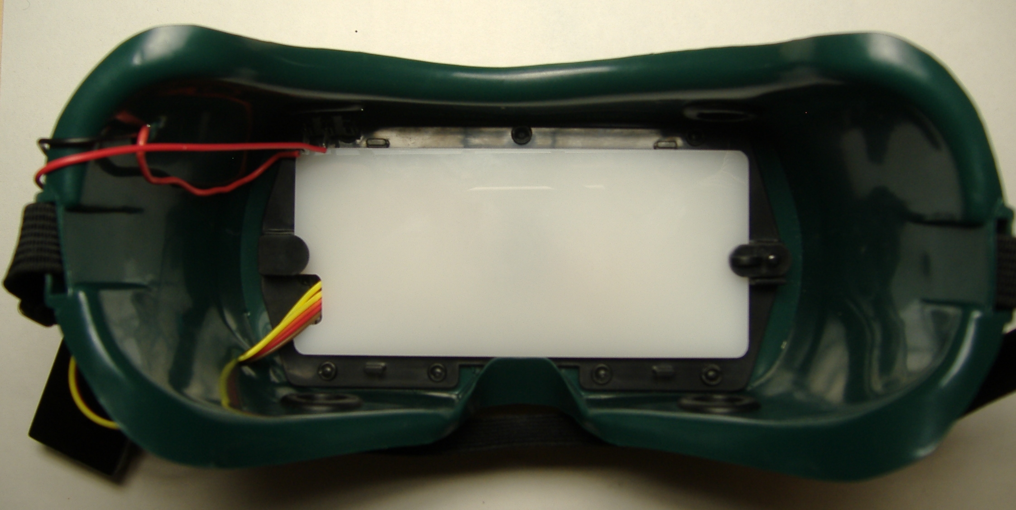
media/photos/DSCF3269.JPG
