michaelerule/goggles/media/photos/DSCF3270.JPG

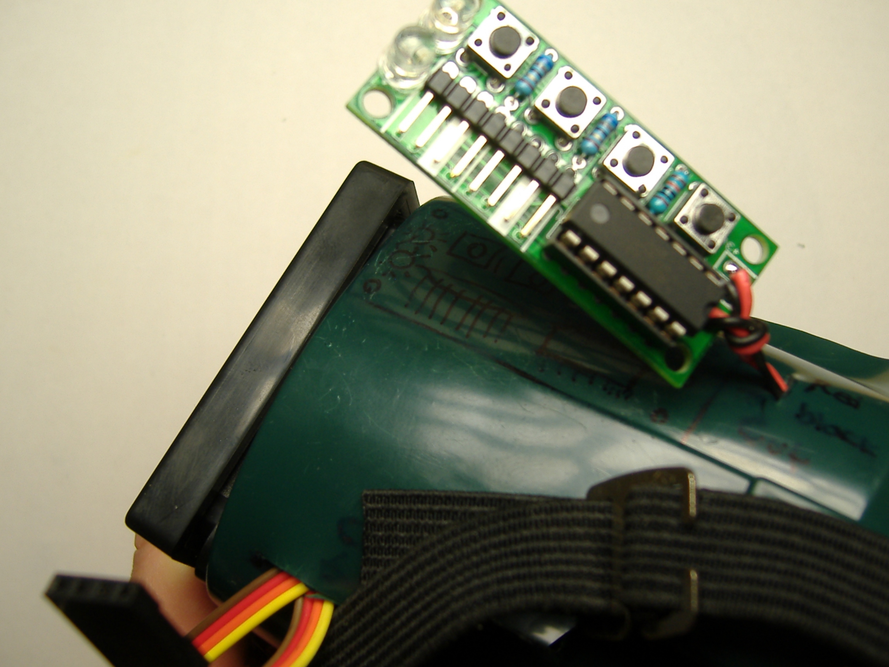
media/photos/DSCF3270.JPG
