michaelerule/goggles/media/photos/DSCF3271.JPG

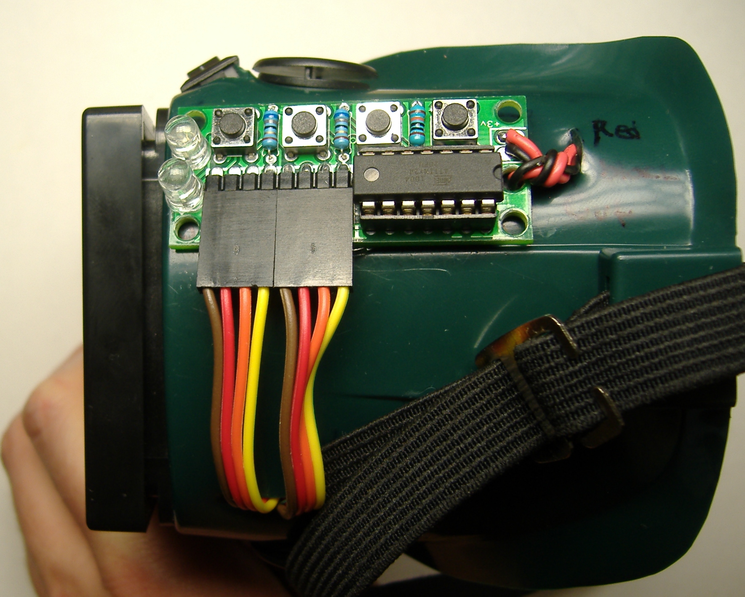
media/photos/DSCF3271.JPG
