michaelerule/goggles/media/photos/DSCF3273.JPG

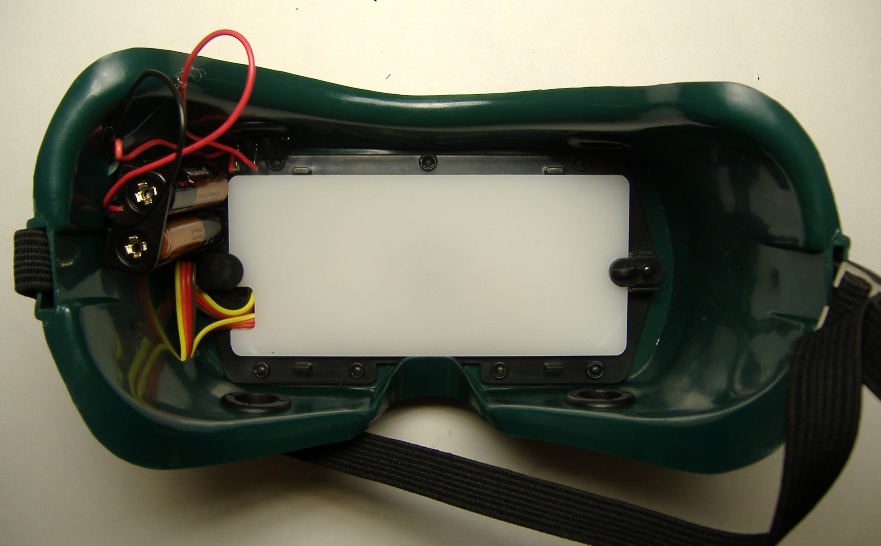
media/photos/DSCF3273.JPG
