michaelerule/goggles/media/photos/DSCF3275.JPG

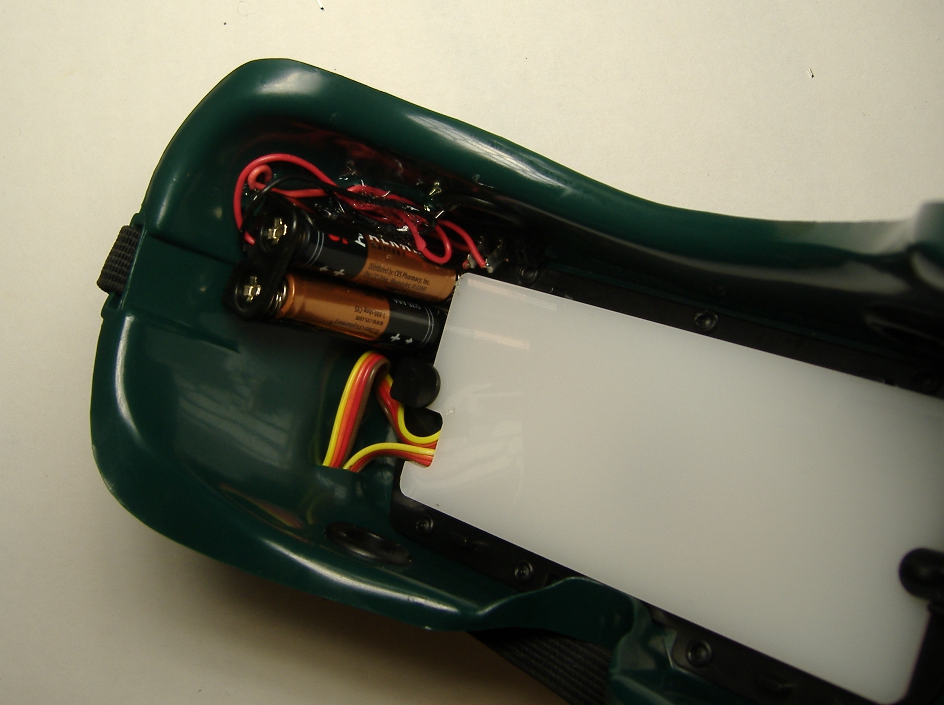
media/photos/DSCF3275.JPG
