michaelerule/goggles/media/photos/DSCF3279.JPG

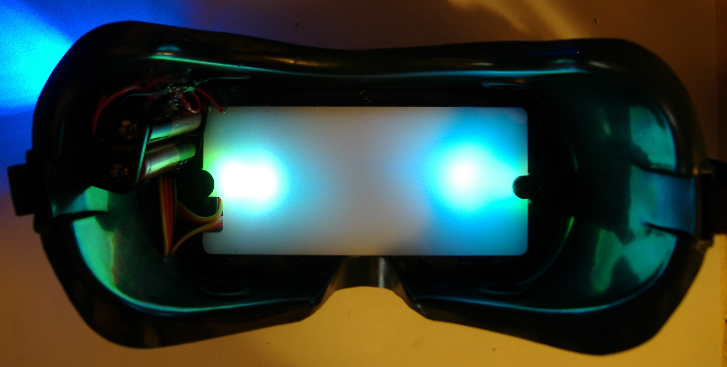
media/photos/DSCF3279.JPG
