michaelerule/goggles/media/photos/DSCF3280.JPG

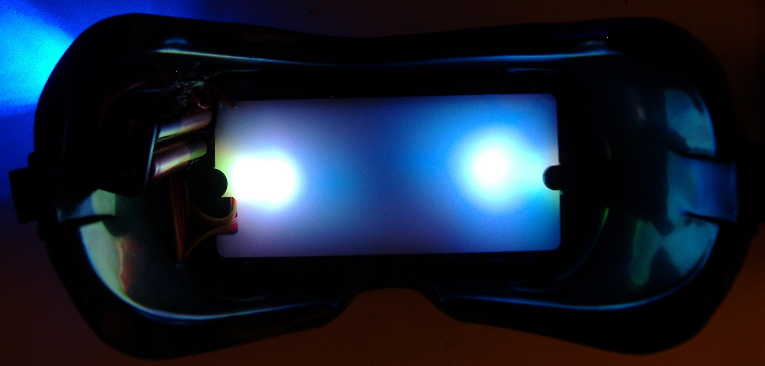
media/photos/DSCF3280.JPG
