michaelerule/goggles/media/photos/DSCF3281.JPG

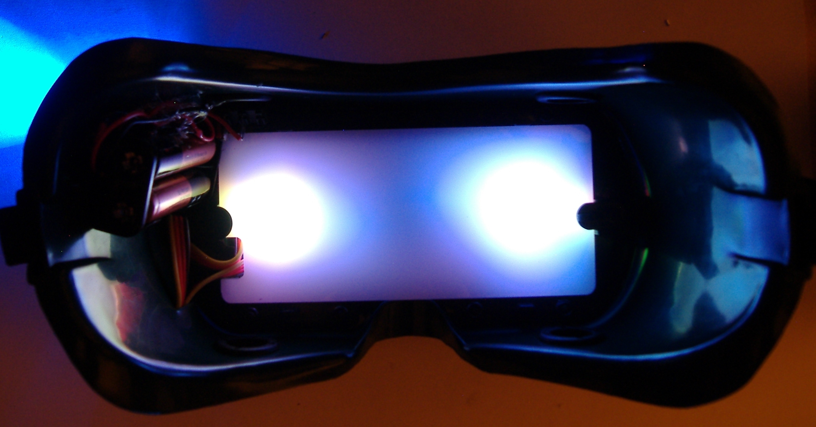
media/photos/DSCF3281.JPG
