michaelerule/goggles/media/photos/DSCF3284.JPG

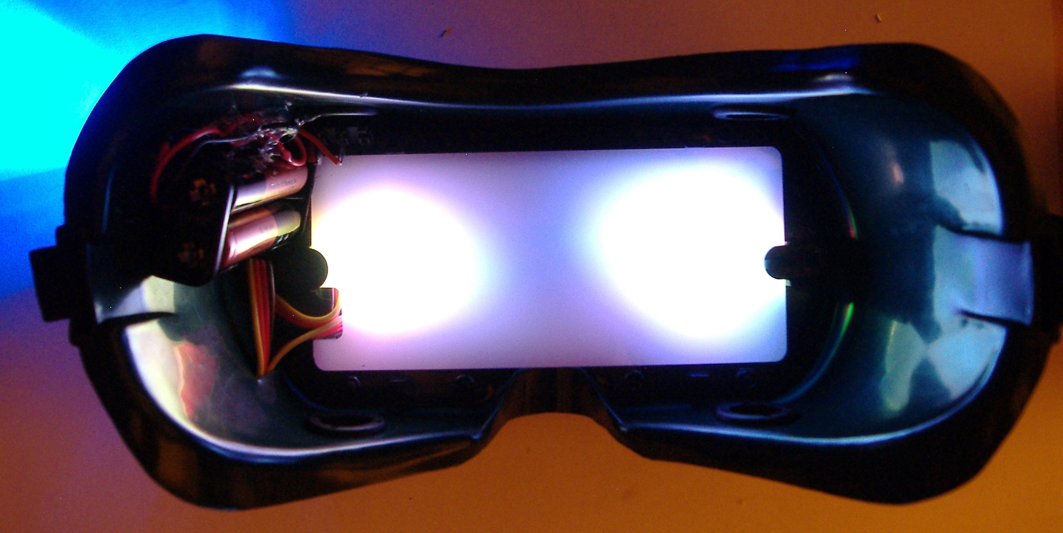
media/photos/DSCF3284.JPG
