michaelerule/goggles/media/visor media/art/out3-30865.png

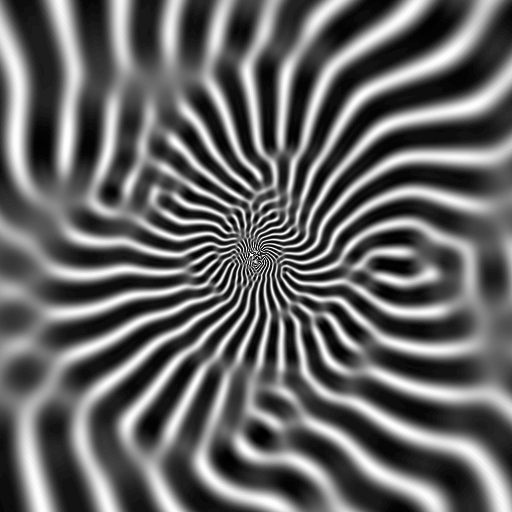
media/visor media/art/out3-30865.png
