michaelerule/goggles/media/visor media/art/out30209.png

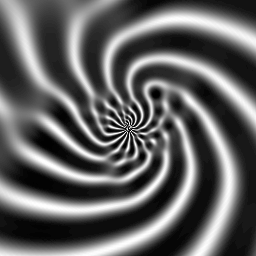
media/visor media/art/out30209.png
