michaelerule/goggles/tools/ee cheatsheet/media/led_tech-gi-1.gif

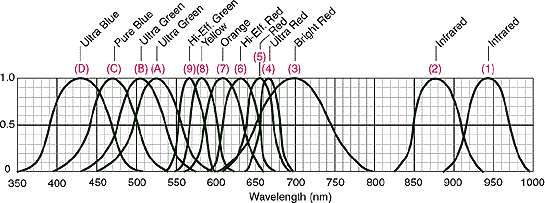
tools/ee cheatsheet/media/led_tech-gi-1.gif
