michaelerule/goggles/tools/ee cheatsheet/media/Technical LED Color Chart_files/25044_large.jpg

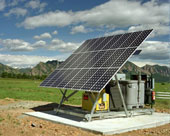
tools/ee cheatsheet/media/Technical LED Color Chart_files/25044_large.jpg
