michaelerule/goggles/tools/ee cheatsheet/media/Technical LED Color Chart_files/102953-specs2_large.jpg

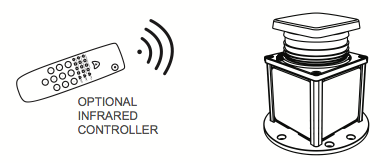
tools/ee cheatsheet/media/Technical LED Color Chart_files/102953-specs2_large.jpg
