michaelerule/goggles/tools/ee cheatsheet/media/Technical LED Color Chart_files/103419_large.jpg

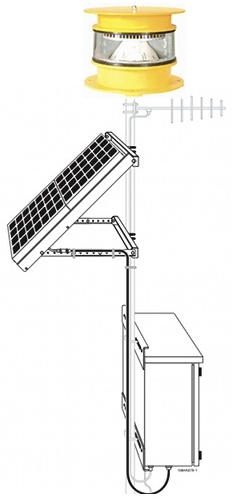
tools/ee cheatsheet/media/Technical LED Color Chart_files/103419_large.jpg
