michaelerule/goggles/tools/ee cheatsheet/media/Technical LED Color Chart_files/105010_specs_drawing_large.jpg

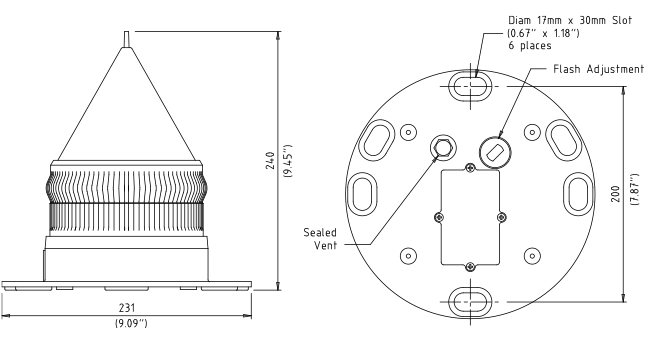
tools/ee cheatsheet/media/Technical LED Color Chart_files/105010_specs_drawing_large.jpg
