michaelerule/goggles/tools/ee cheatsheet/media/Technical LED Color Chart_files/105010_specs_pic_large.jpg

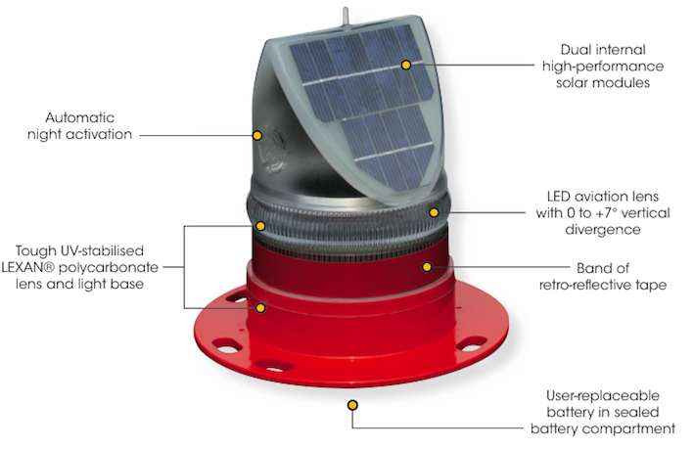
tools/ee cheatsheet/media/Technical LED Color Chart_files/105010_specs_pic_large.jpg
