michaelerule/goggles/tools/ee cheatsheet/media/Technical LED Color Chart_files/105011-k_large.jpg

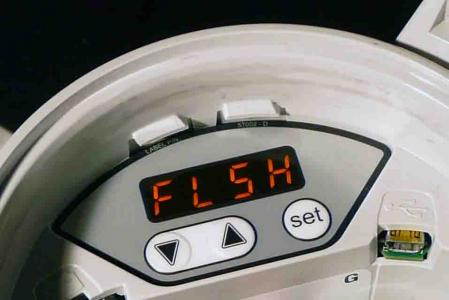
tools/ee cheatsheet/media/Technical LED Color Chart_files/105011-k_large.jpg
