michaelerule/goggles/tools/ee cheatsheet/media/Technical LED Color Chart_files/105011-l_large.jpg

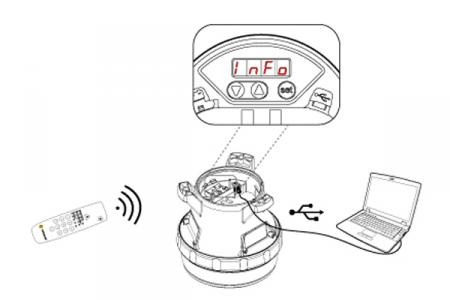
tools/ee cheatsheet/media/Technical LED Color Chart_files/105011-l_large.jpg
