michaelerule/goggles/tools/ee cheatsheet/media/Technical LED Color Chart_files/105011_drawing_large.jpg

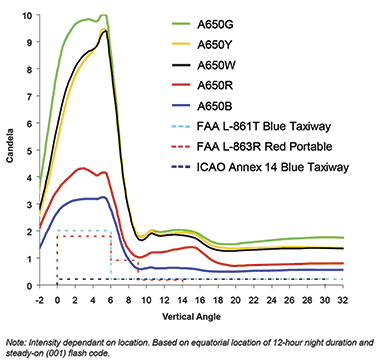
tools/ee cheatsheet/media/Technical LED Color Chart_files/105011_drawing_large.jpg
