michaelerule/goggles/tools/ee cheatsheet/media/Technical LED Color Chart_files/160400-specs_large.jpg

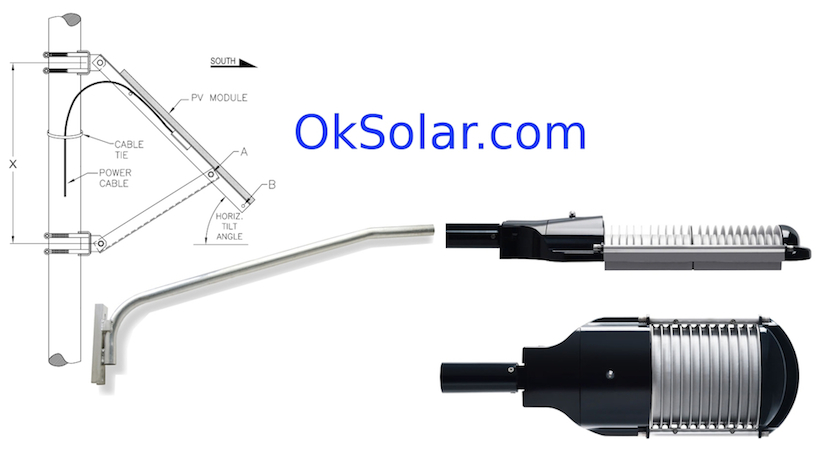
tools/ee cheatsheet/media/Technical LED Color Chart_files/160400-specs_large.jpg
