michaelerule/goggles/tools/ee cheatsheet/media/Technical LED Color Chart_files/0167024_large.jpg

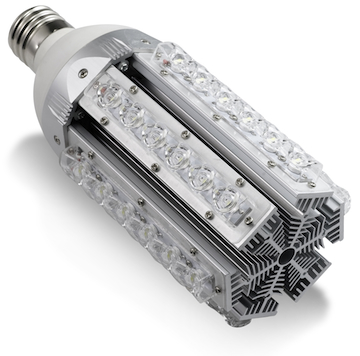
tools/ee cheatsheet/media/Technical LED Color Chart_files/0167024_large.jpg
