michaelerule/goggles/tools/ee cheatsheet/media/Technical LED Color Chart_files/1029684-specs1_large.jpg

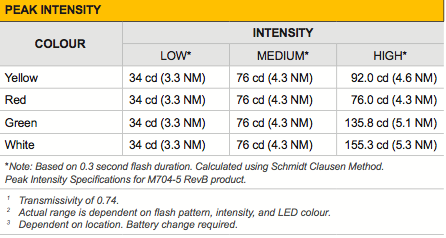
tools/ee cheatsheet/media/Technical LED Color Chart_files/1029684-specs1_large.jpg
