michaelerule/goggles/tools/ee cheatsheet/media/Technical LED Color Chart_files/1029684-specs3_large.jpg

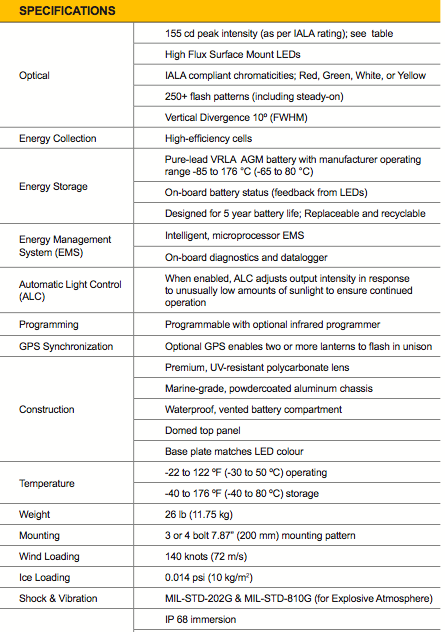
tools/ee cheatsheet/media/Technical LED Color Chart_files/1029684-specs3_large.jpg
