michaelerule/goggles/tools/ee cheatsheet/media/Technical LED Color Chart_files/led_tech-49-2.jpg

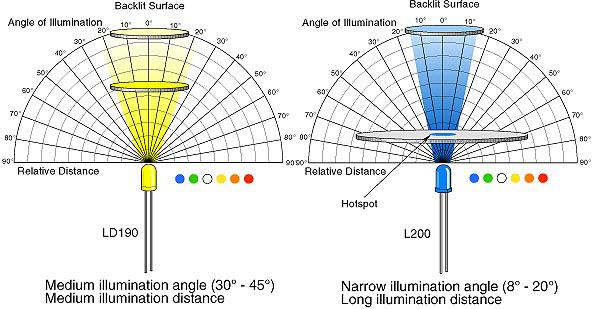
tools/ee cheatsheet/media/Technical LED Color Chart_files/led_tech-49-2.jpg
