michaelerule/goggles/tools/ee cheatsheet/media/Technical LED Color Chart_files/led_tech-gi-2.gif

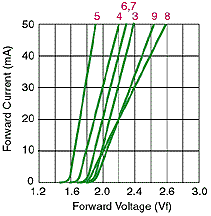
tools/ee cheatsheet/media/Technical LED Color Chart_files/led_tech-gi-2.gif
