michaelerule/goggles/tools/ee cheatsheet/media/Technical LED Color Chart_files/marine_solar_Light_M650_Peak_Intensity_Table.jpg

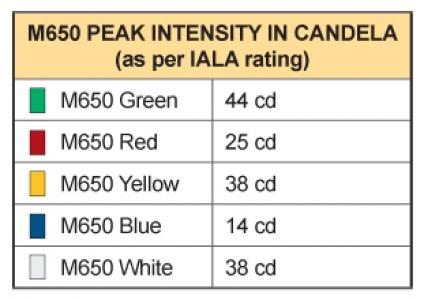
tools/ee cheatsheet/media/Technical LED Color Chart_files/marine_solar_Light_M650_Peak_Intensity_Table.jpg
