michaelerule/goggles/tools/ee cheatsheet/media/Technical LED Color Chart_files/watermarked 11077_small.png

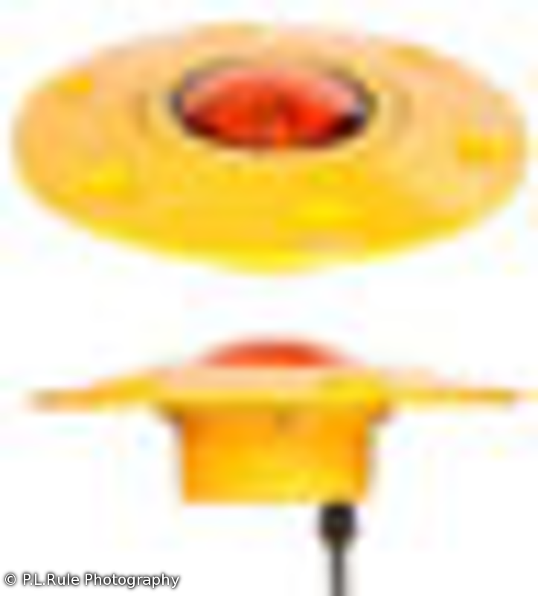
tools/ee cheatsheet/media/Technical LED Color Chart_files/watermarked 11077_small.png
