michaelerule/goggles/tools/ee cheatsheet/media/Technical LED Color Chart_files/watermarked 102933-specs7_large.png

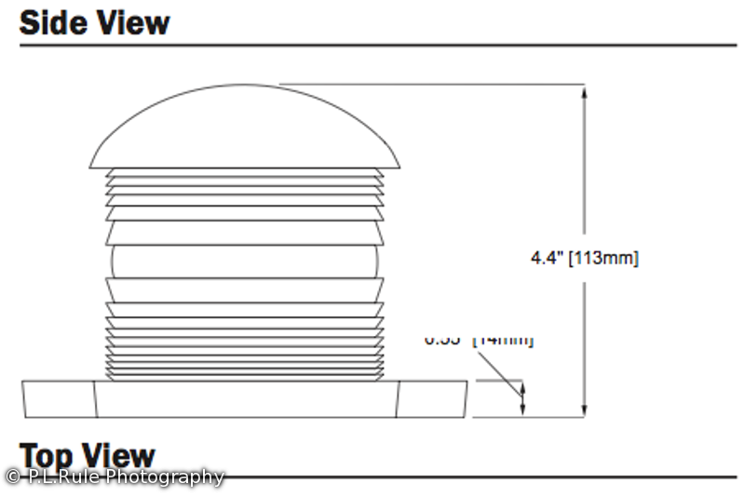
tools/ee cheatsheet/media/Technical LED Color Chart_files/watermarked 102933-specs7_large.png
