michaelerule/goggles/tools/ee cheatsheet/media/Technical LED Color Chart_files/watermarked 105011-j_large.png

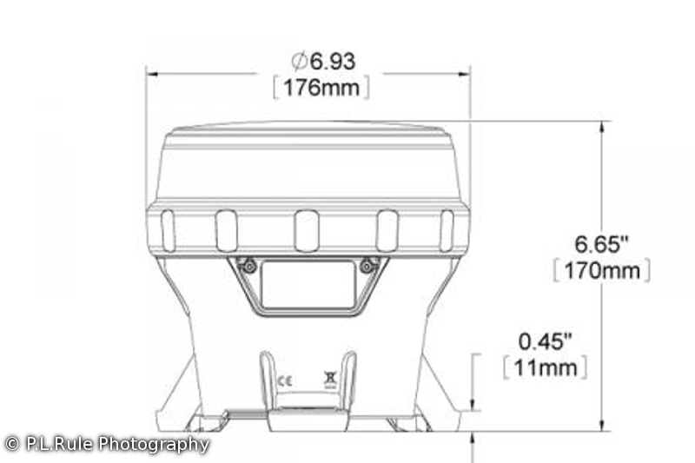
tools/ee cheatsheet/media/Technical LED Color Chart_files/watermarked 105011-j_large.png
