michaelerule/goggles/tools/ee cheatsheet/media/Technical LED Color Chart_files/watermarked 724900_large.png

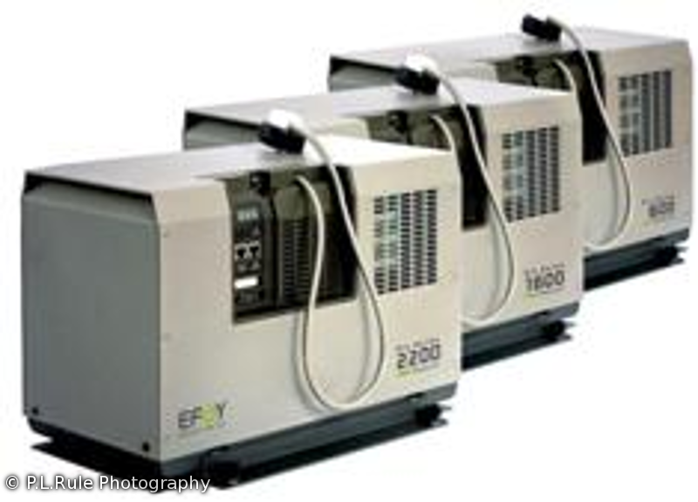
tools/ee cheatsheet/media/Technical LED Color Chart_files/watermarked 724900_large.png
