michaelerule/goggles/tools/ee cheatsheet/media/Technical LED Color Chart_files/watermarked 1119600_small.png

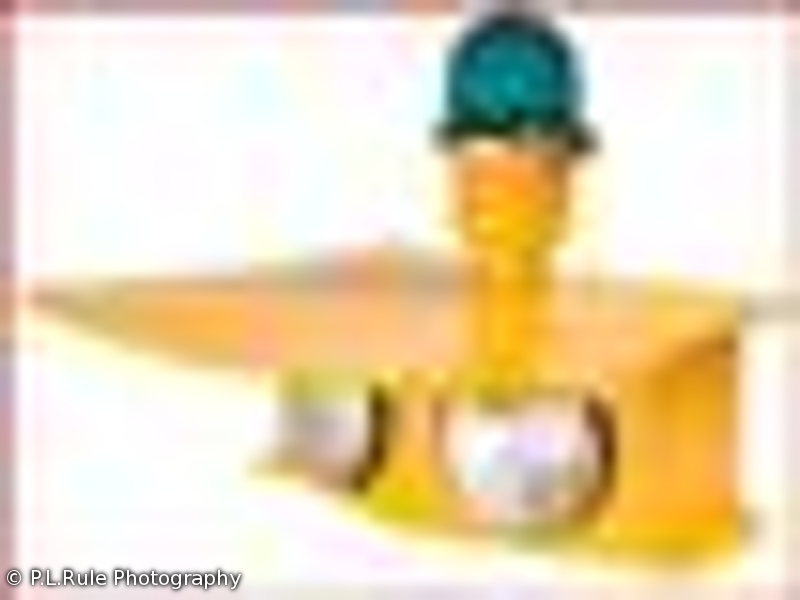
tools/ee cheatsheet/media/Technical LED Color Chart_files/watermarked 1119600_small.png
