michaelerule/goggles/tools/ee cheatsheet/media/Technical LED Color Chart_files/watermarked 25070777_large.png

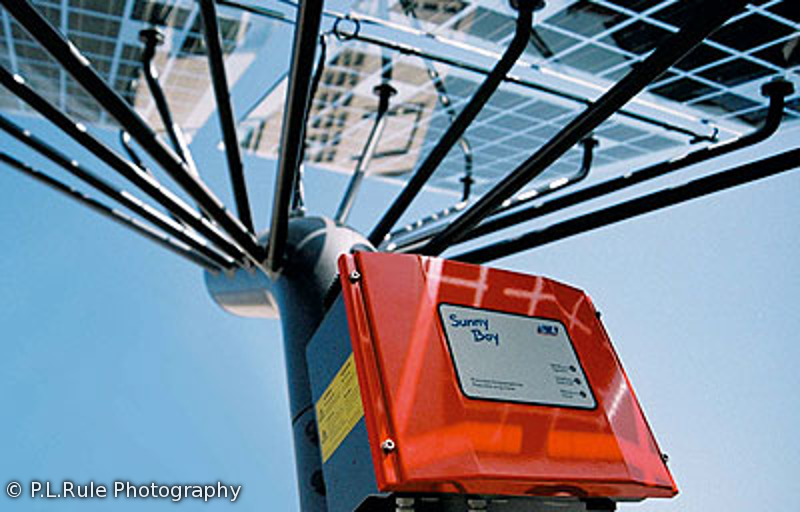
tools/ee cheatsheet/media/Technical LED Color Chart_files/watermarked 25070777_large.png
