michaelerule/goggles/tools/ee cheatsheet/media/Technical LED Color Chart_files/watermarked automation_din-rail_large.png

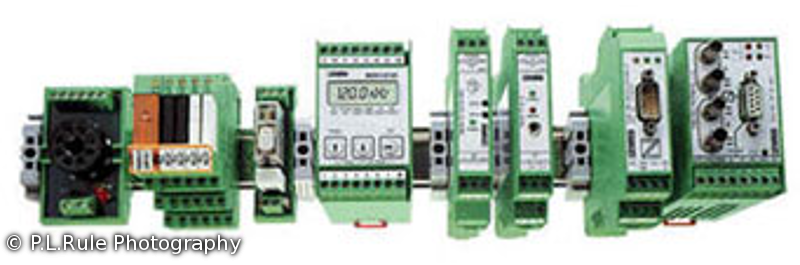
tools/ee cheatsheet/media/Technical LED Color Chart_files/watermarked automation_din-rail_large.png
