michaelerule/goggles/tools/ee cheatsheet/media/Technical LED Color Chart_files/watermarked explosionproof-camera-enclosure.png

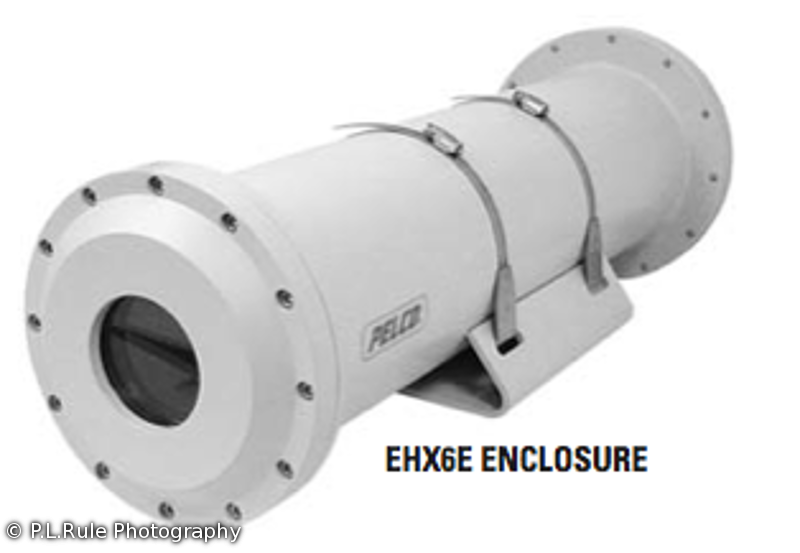
tools/ee cheatsheet/media/Technical LED Color Chart_files/watermarked explosionproof-camera-enclosure.png
