michaelerule/goggles/tools/ee cheatsheet/media/Technical LED Color Chart_files/watermarked get-a-quote.png

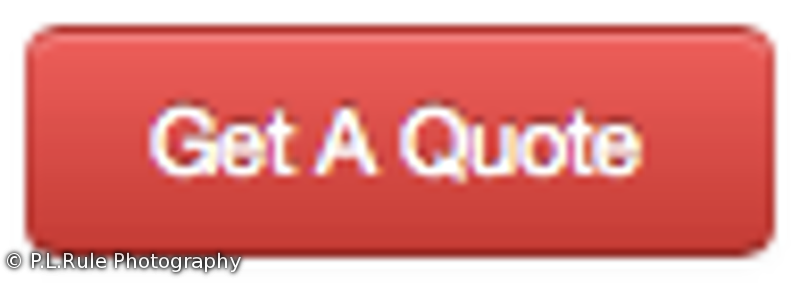
tools/ee cheatsheet/media/Technical LED Color Chart_files/watermarked get-a-quote.png
