michaelerule/goggles/tools/ee cheatsheet/media/Technical LED Color Chart_files/watermarked information.png

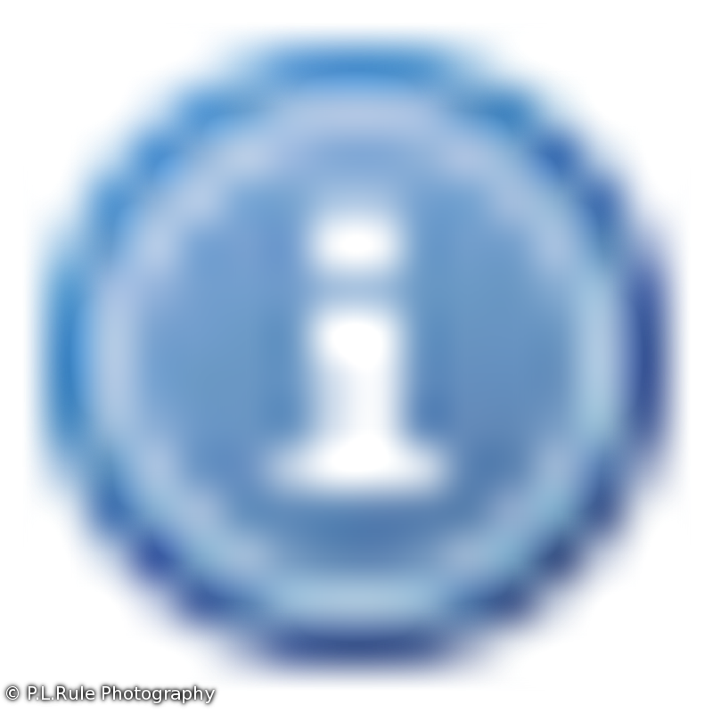
tools/ee cheatsheet/media/Technical LED Color Chart_files/watermarked information.png
