michaelerule/goggles/tools/ee cheatsheet/media/Technical LED Color Chart_files/watermarked led_tech-49-1.png

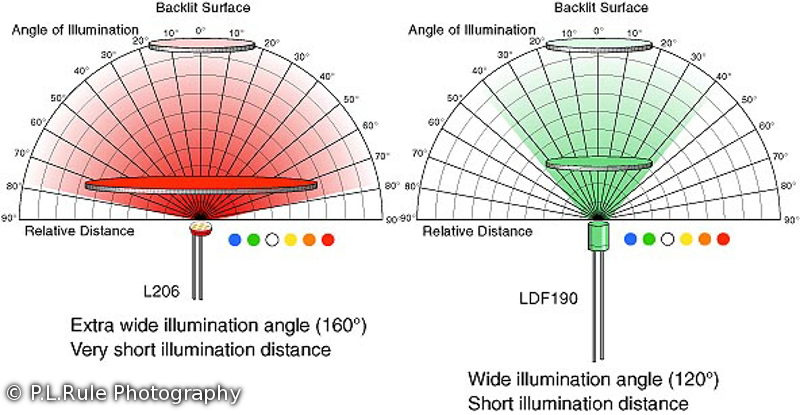
tools/ee cheatsheet/media/Technical LED Color Chart_files/watermarked led_tech-49-1.png
