michaelerule/goggles/tools/ee cheatsheet/howtolearnemacs/howtolearnemacs.odt

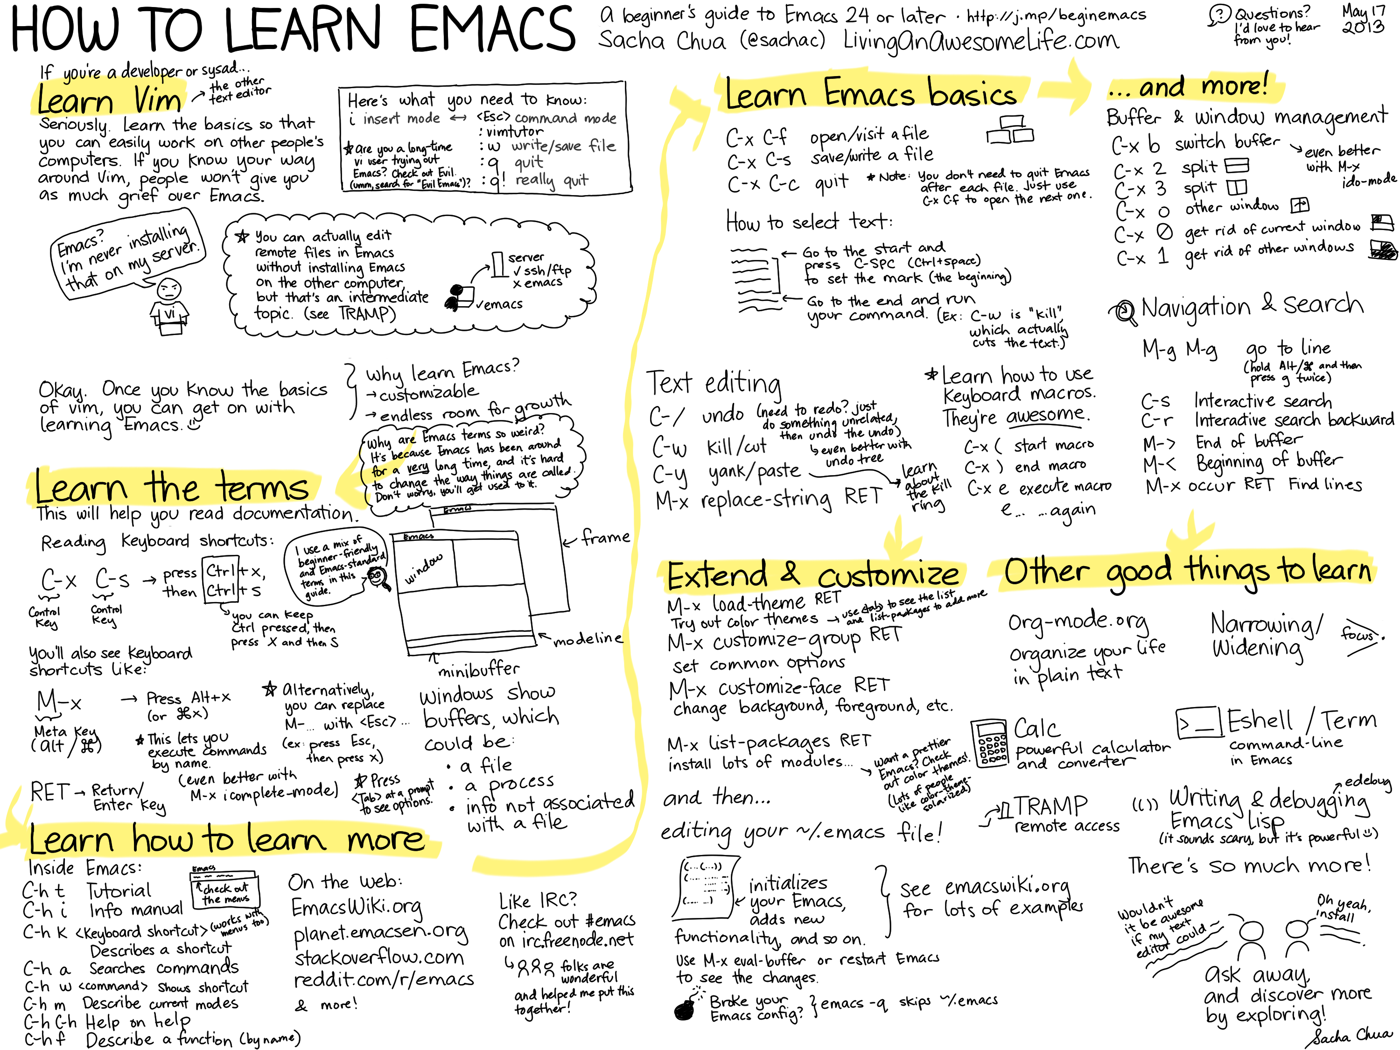
[picture p166: figure]
