michaelerule/goggles/media/visor media/assemble/DSCF3150 (copy).JPG

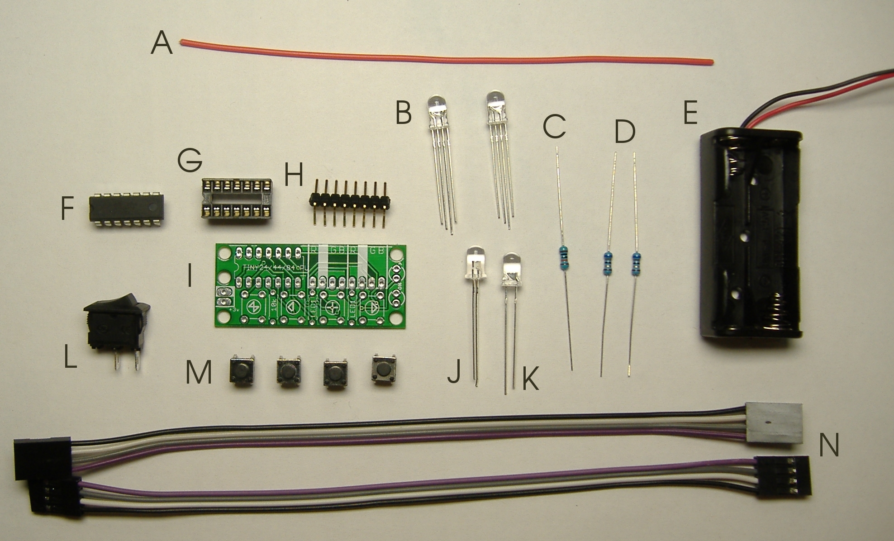
media/visor media/assemble/DSCF3150 (copy).JPG
