michaelerule/goggles/media/visor media/assemble/DSCF3159.JPG

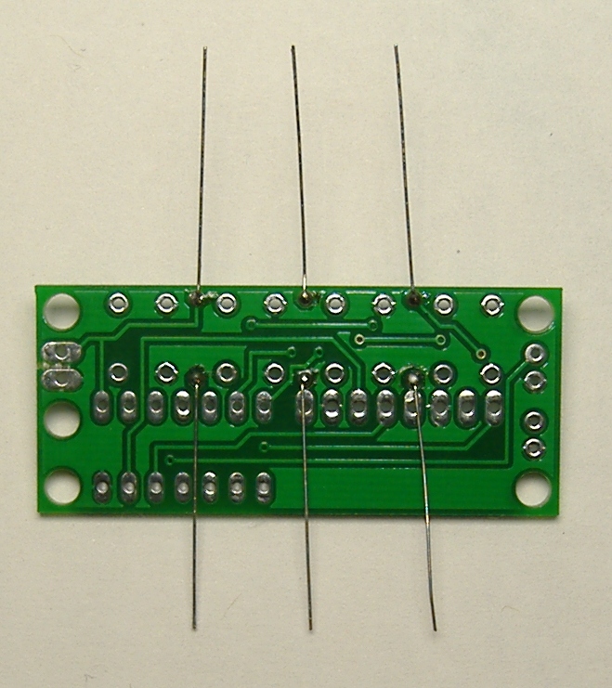
media/visor media/assemble/DSCF3159.JPG
