michaelerule/goggles/media/visor media/assemble/DSCF3161.JPG

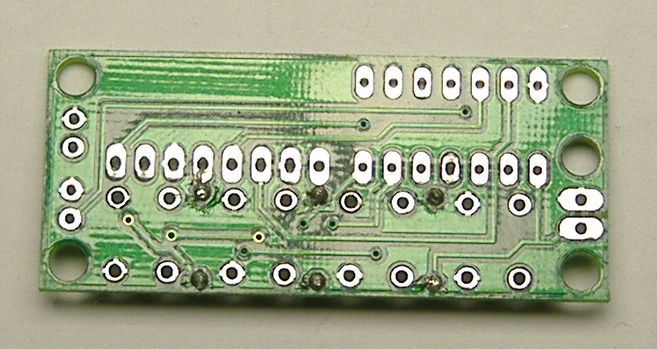
media/visor media/assemble/DSCF3161.JPG
