michaelerule/goggles/media/visor media/assemble/DSCF3178.JPG

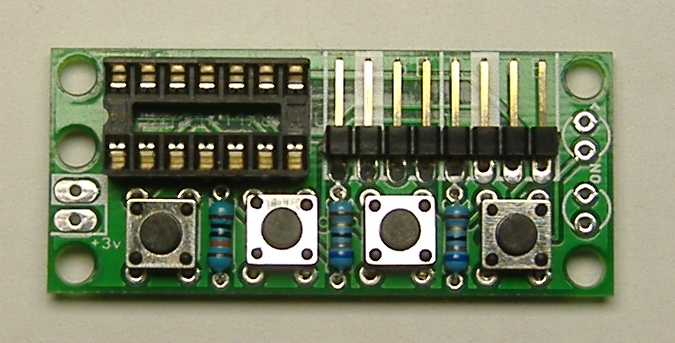
media/visor media/assemble/DSCF3178.JPG
