michaelerule/goggles/media/visor media/assemble/DSCF3187.JPG

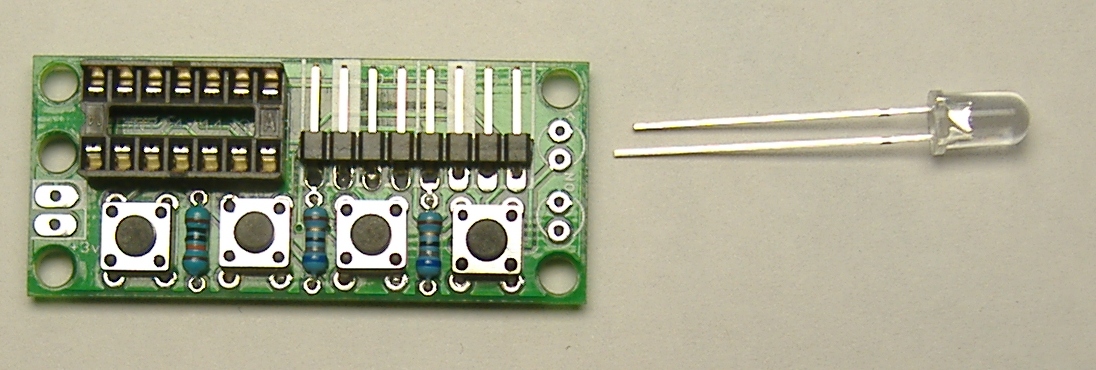
media/visor media/assemble/DSCF3187.JPG
