michaelerule/goggles/media/visor media/assemble/DSCF3189.JPG

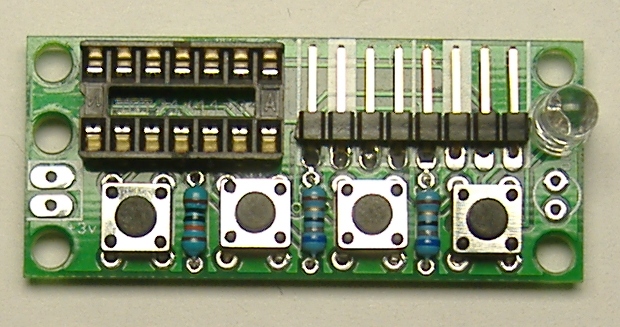
media/visor media/assemble/DSCF3189.JPG
