michaelerule/goggles/media/visor media/assemble/DSCF3191.JPG

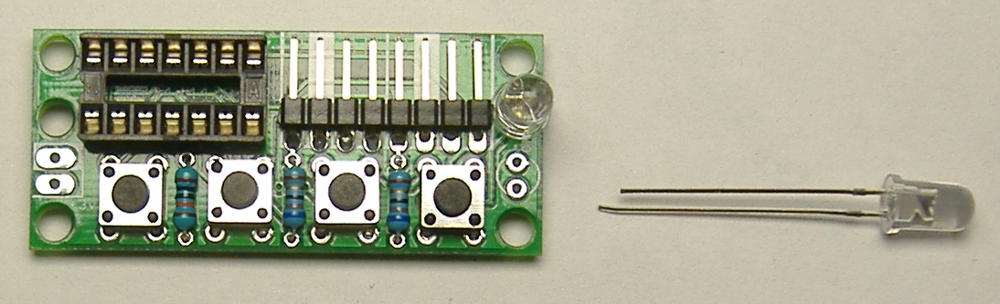
media/visor media/assemble/DSCF3191.JPG
