michaelerule/goggles/media/visor media/assemble/DSCF3196.JPG

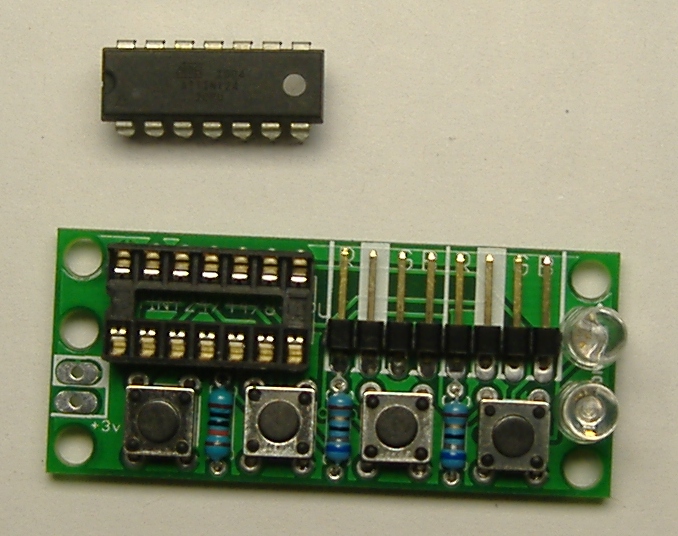
media/visor media/assemble/DSCF3196.JPG
