michaelerule/goggles/media/visor media/assemble/DSCF3204.JPG

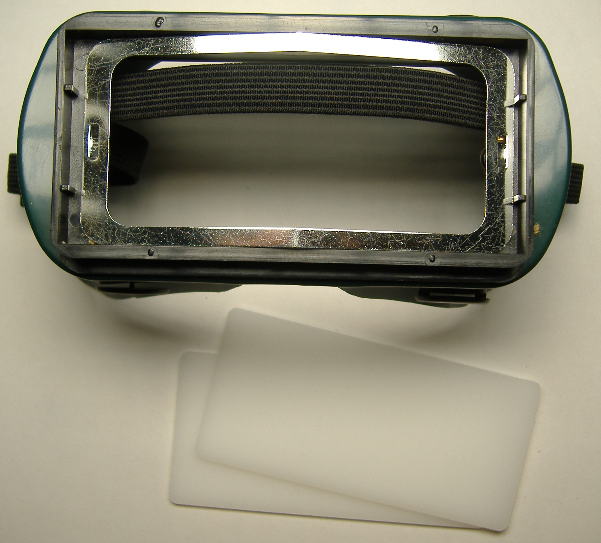
media/visor media/assemble/DSCF3204.JPG
