michaelerule/goggles/media/visor media/assemble/DSCF3217.JPG

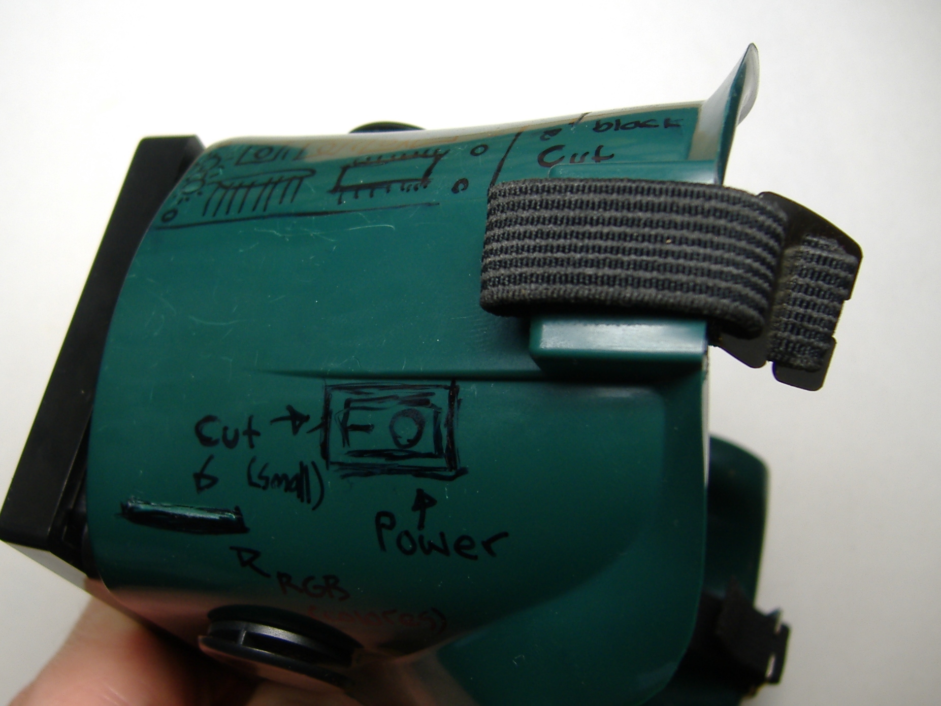
media/visor media/assemble/DSCF3217.JPG
