michaelerule/goggles/media/visor media/assemble/DSCF3223.JPG

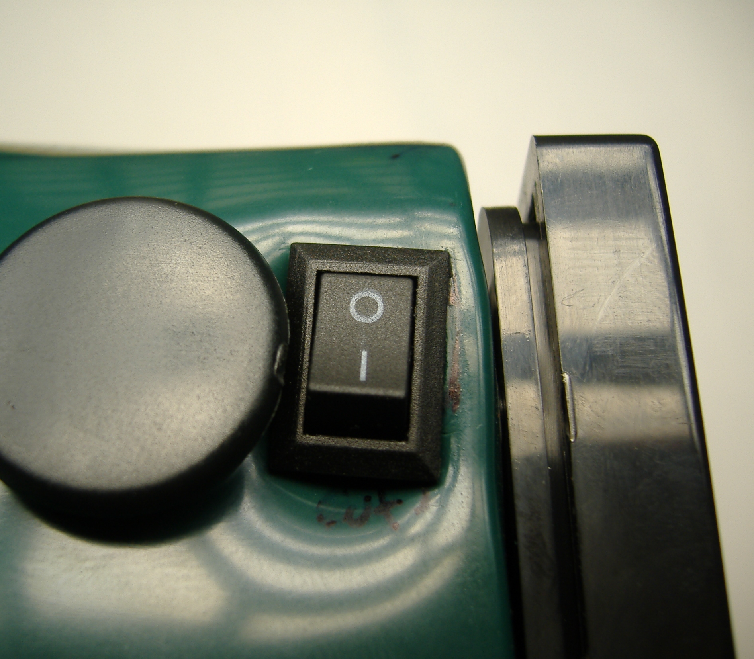
media/visor media/assemble/DSCF3223.JPG
