michaelerule/goggles/media/visor media/assemble/DSCF3224.JPG

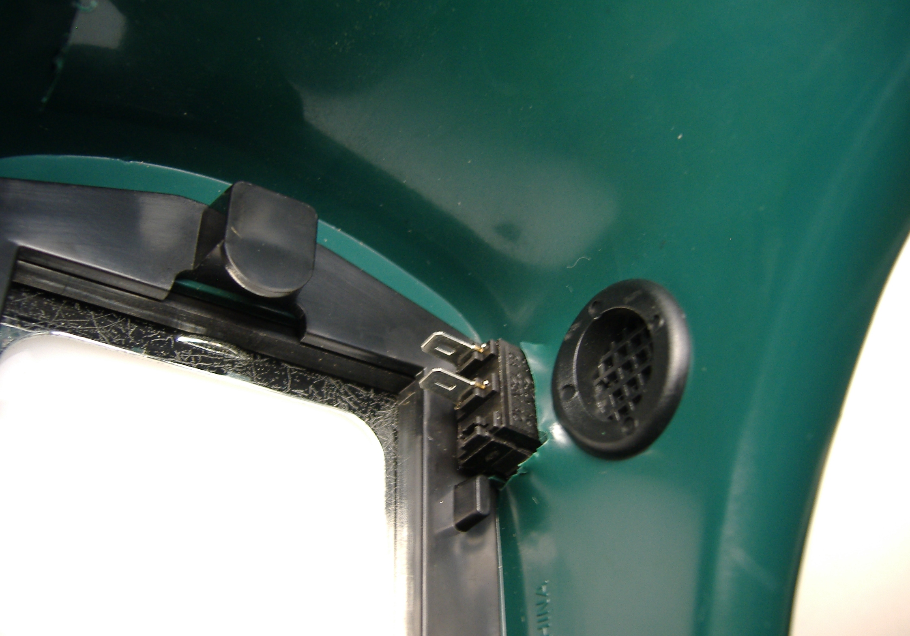
media/visor media/assemble/DSCF3224.JPG
