michaelerule/goggles/media/visor media/assemble/DSCF3225.JPG

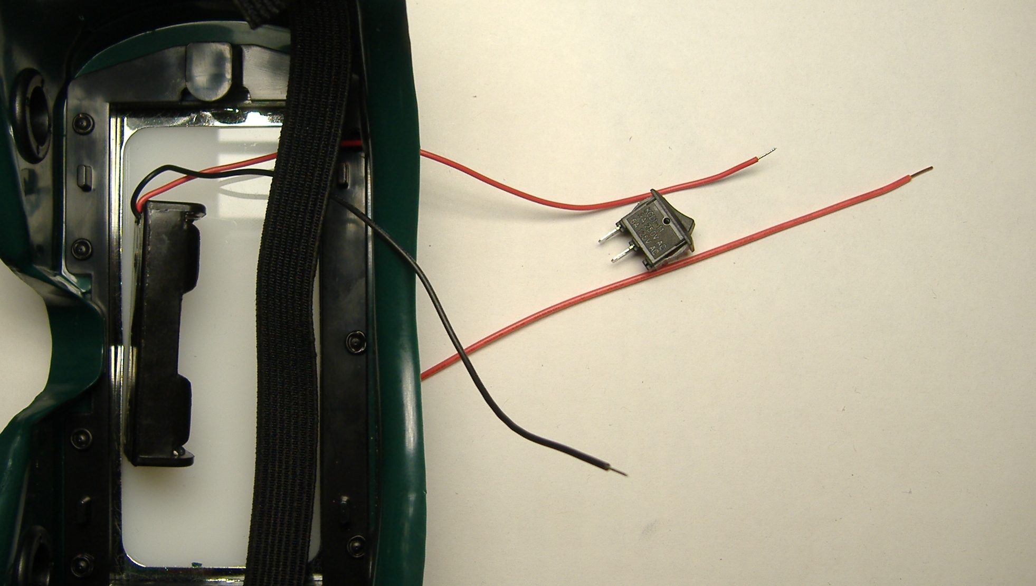
media/visor media/assemble/DSCF3225.JPG
