michaelerule/goggles/media/visor media/assemble/DSCF3227.JPG

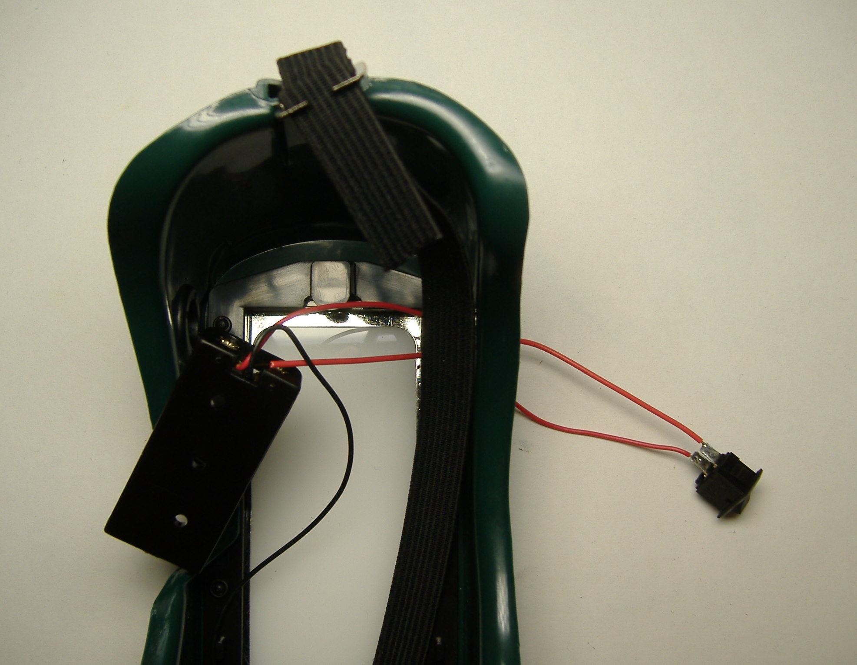
media/visor media/assemble/DSCF3227.JPG
