michaelerule/goggles/media/visor media/assemble/DSCF3240.JPG

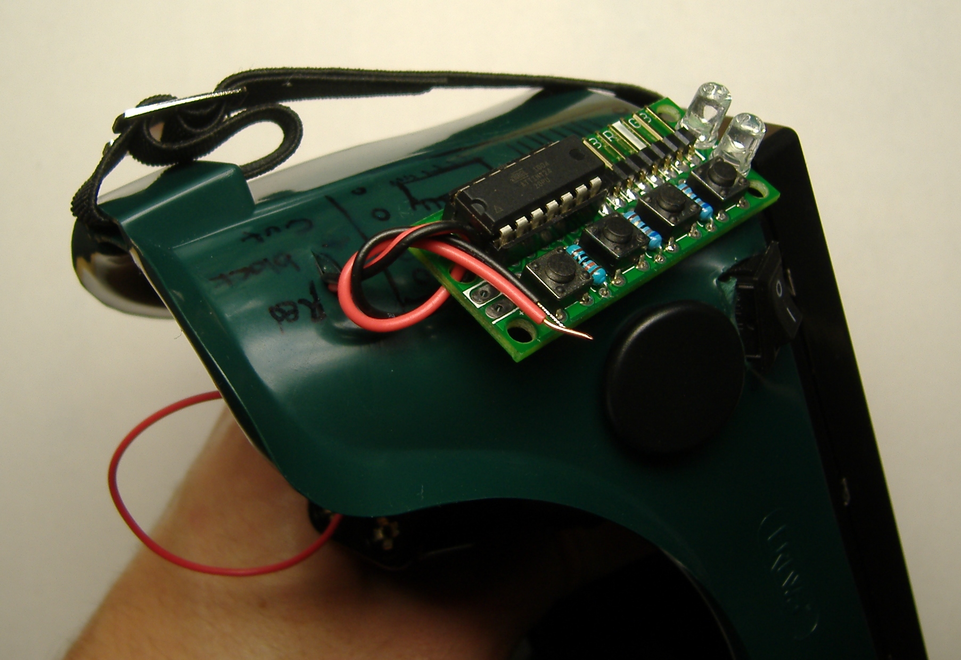
media/visor media/assemble/DSCF3240.JPG
