michaelerule/goggles/media/visor media/assemble/DSCF3241.JPG

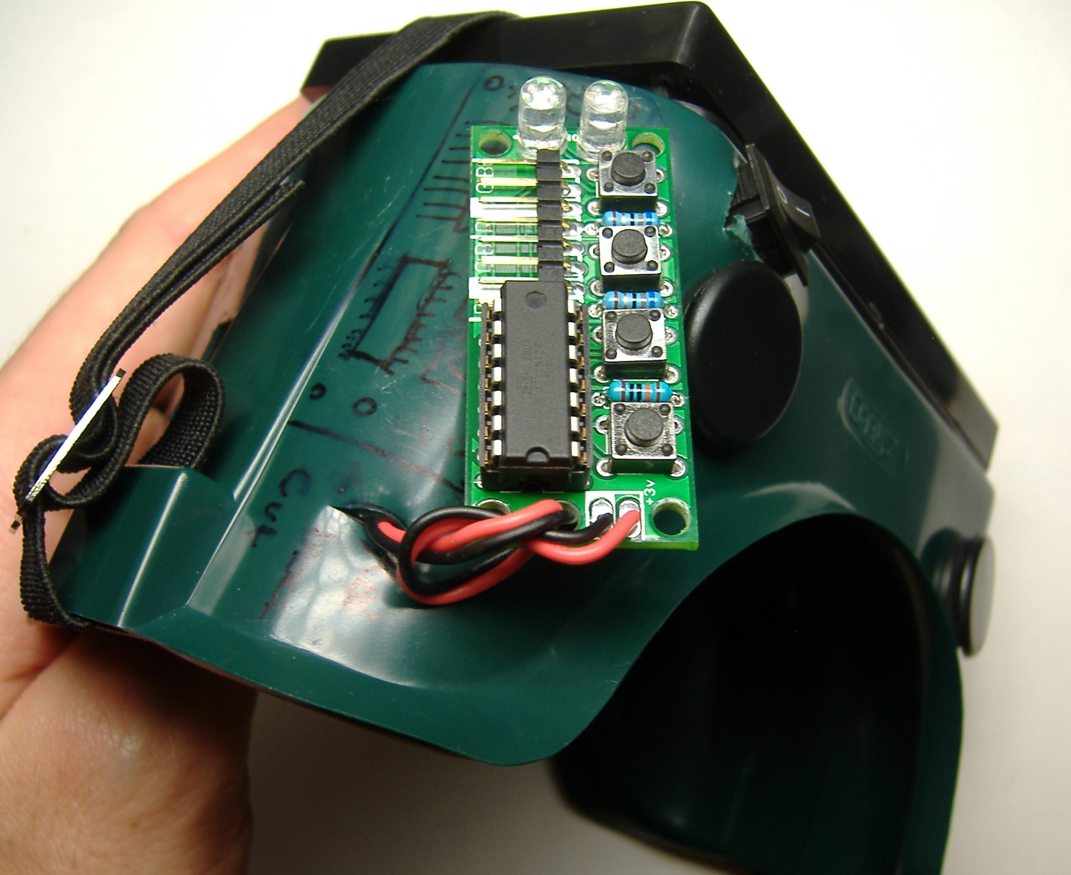
media/visor media/assemble/DSCF3241.JPG
