michaelerule/goggles/media/visor media/assemble/DSCF3243.JPG

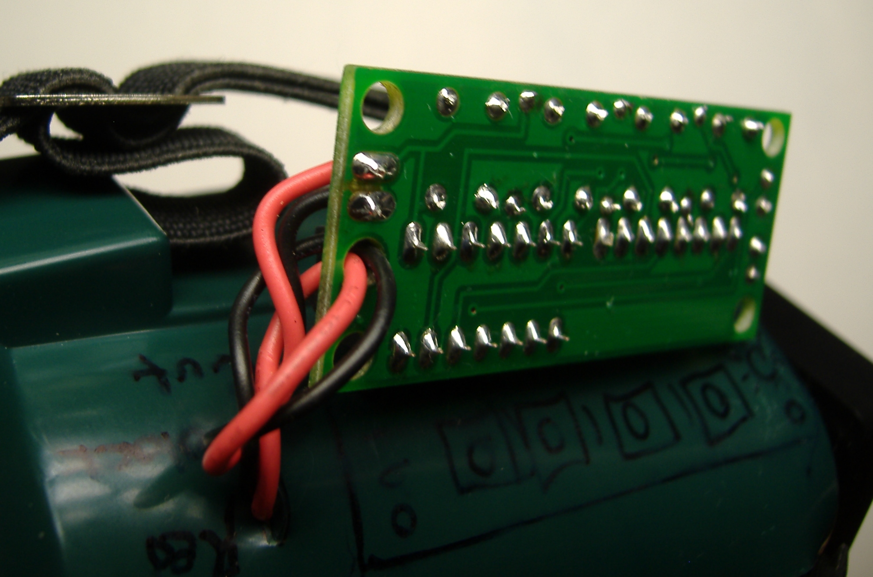
media/visor media/assemble/DSCF3243.JPG
