michaelerule/goggles/media/visor media/assemble/DSCF3244.JPG

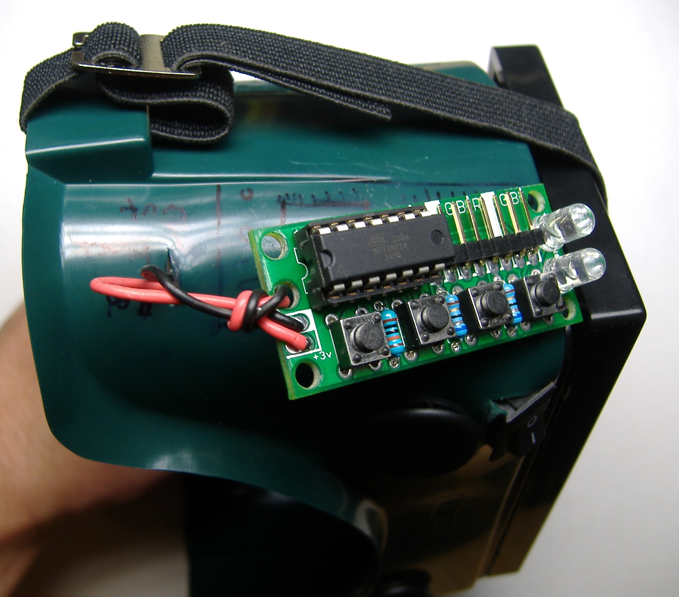
media/visor media/assemble/DSCF3244.JPG
