michaelerule/goggles/media/visor media/assemble/DSCF3251.JPG

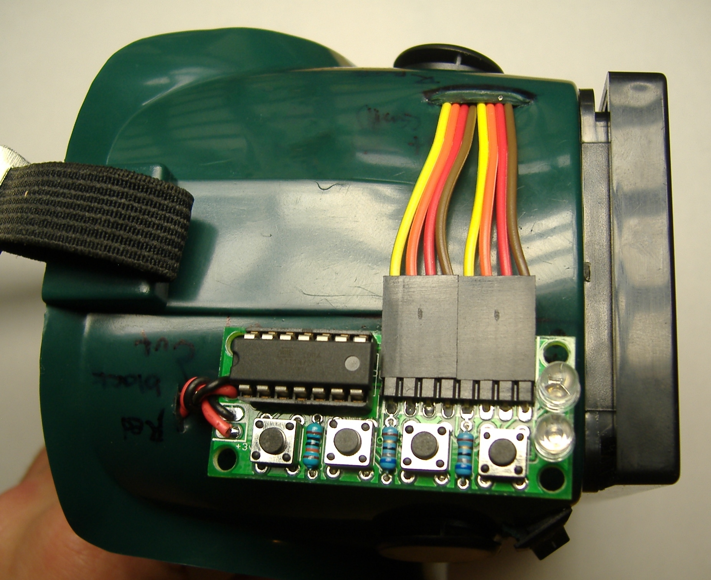
media/visor media/assemble/DSCF3251.JPG
