michaelerule/goggles/media/visor media/assemble/DSCF3265.JPG

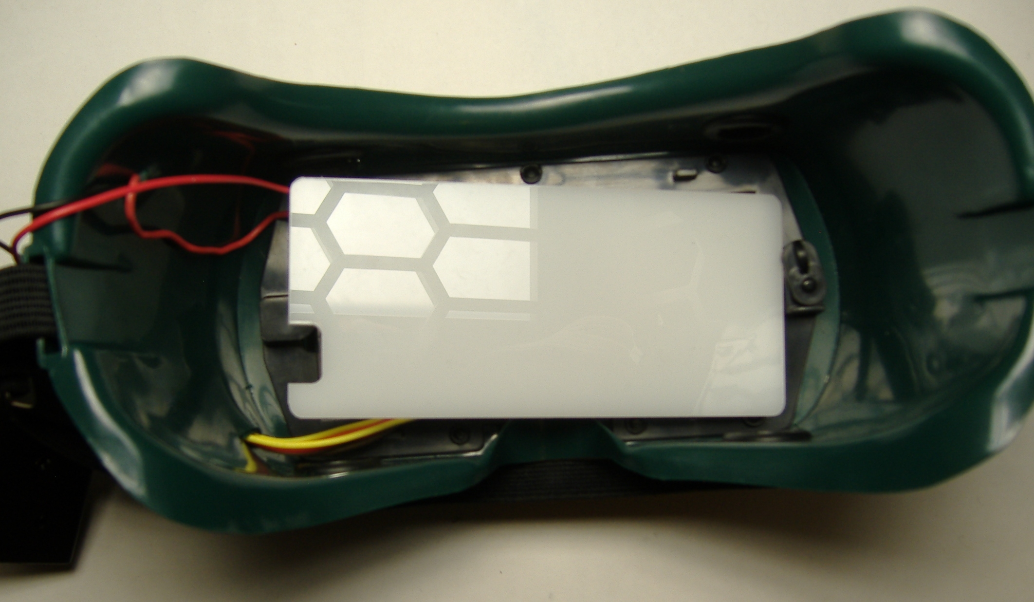
media/visor media/assemble/DSCF3265.JPG
