michaelerule/goggles/tools/ee cheatsheet/LED.pdf

## LED and resistor cheat sheet

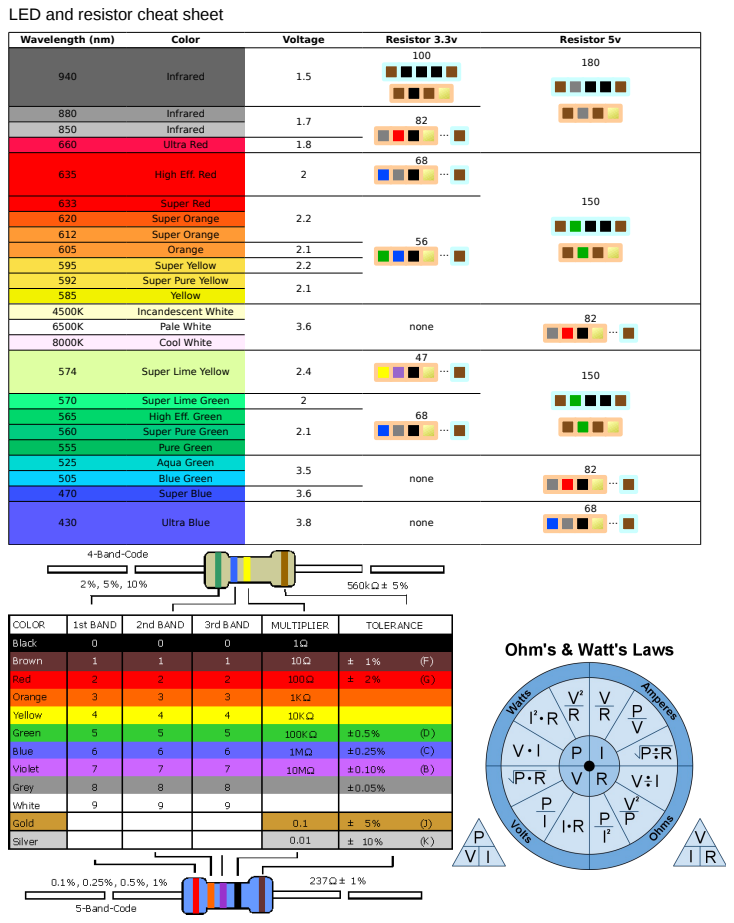
[picture p187: page 1]
Wavelength (nm); Color; Voltage; Resistor 3.3v; Resistor 5v; Infrared; Ultra Red; High Eff. Red; Super Red; Super Orange; Orange; Super Yellow; Super Pure Yellow; Yellow; Incandescent White; none; Pale White; Cool White; Super Lime Yellow; Super Lime Green; High Eff. Green; Super Pure Green; Pure Green; Aqua Green; Blue Green; Super Blue; Ultra Blue
